pardhuvarmax/Project-Ouroboros/BluePill/Documentations/Ouroboros Roles Doc.pdf

# Project Ouroboros – Roles & Responsibilities Document

## Overview

Project Ouroboros is a dual-nature cybersecurity + hardware + AI initiative that embodies the eternal cycle of attack and defense, inspired by the mythological serpent Ouroboros. To ensure the successful execution of this project, clear roles and responsibilities are essential across technical, strategic, and business domains.

This document defines all roles required for the development, launch, and scaling of Project Ouroboros, with responsibilities spanning hardware, software, AI, research, community engagement, and commercialization.

## 1. Leadership & Governance

Project Lead (Founder / Visionary)

Define overall vision and mission of Project Ouroboros.
Oversee both defensive and offensive components, ensuring balance. Make final decisions on product scope, direction, and partnerships. Maintain philosophical and mythological branding rooted in Ouroboros. Ensure legal and ethical compliance.
Advisory Board (Mentors / Senior Experts)

Provide expert advice on cybersecurity, hardware, AI, and product strategy. Ensure project aligns with academic, industrial, and ethical standards. Connect with investors, Kickstarter advisors, and community leaders.

## 2. Technical Development

Hardware Engineering Team

Design PCB schematics and layouts for ESP32 + SDR devices. Integrate display modules (OLED, TFT, touchscreen).
Ensure low-cost, reliable builds for Kickstarter scalability. Prototype RF-based tools (BLE sniffer, Sub-GHz jammer, etc.). Firmware Development Team

Develop embedded C / Arduino / MicroPython firmware for ESP32. Implement features:
Wi-Fi deauth detector & shield.
Spectrum analyzer (2.4 GHz).

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
BLE sniffing & spoof detection.
RF scanning & replay attack modules.
Optimize for low power consumption and smooth real-time graphs. Software & AI Development Team

Build AI-based anomaly detection models (TinyML on-device or cloud). Develop companion mobile/desktop app for visualization & extended analysis. Implement real-time packet analysis, rogue detection, and network hardening. Secure communication channel between devices and apps.
Cybersecurity Research Team

Research latest Wi-Fi, BLE, Zigbee, Sub-GHz vulnerabilities.
Test and validate offensive tools (beacon spammer, captive portal, replay attacks). Ensure defensive tools are hardened against evolving threats.
Document open-source offensive modules for GitHub community.

## 3. Product & UX

UI/UX Design Team

Create intuitive interfaces for TFT/OLED displays.
Design real-time waterfall graphs for spectrum analyzers. Build smooth UX for mobile companion app.
Ensure defensive device feels professional & consumer-friendly. Product Management

Define roadmap: pre-release, Kickstarter launch, v2 upgrades.
Balance feature sets between defense (consumer market) and offense (research GitHub). Conduct competitor benchmarking (Flipper Zero, Wi-Fi Pineapple, etc.).
Ensure pricing strategy aligns with build cost and market demand.

## 4. Business & Commercialization

Kickstarter Campaign Manager

Develop and manage the crowdfunding campaign.
Create marketing materials, videos, and product storytelling. Manage tiered pricing, stretch goals, and reward structures. Oversee logistics for backer rewards.
Branding & Marketing Team

Create strong brand identity rooted in Ouroboros mythology. Manage social media campaigns, community engagement, and PR. Collaborate with YouTubers, infosec influencers, and educators. Highlight defensive device as consumer-friendly.

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
Sales & Distribution

Handle pre-orders, shipping, and customer support post-Kickstarter. Work with global distributors for scaling production.
Partner with academic institutions & cybersecurity educators.

## 5. Community & Recognition

Open Source Offensive Team

Maintain GitHub repository for offensive research tools. Provide documentation, tutorials, and safe-use guidelines. Encourage collaboration with cybersecurity researchers.
Community Manager

Engage with Kickstarter backers, GitHub contributors, and Discord/Reddit communities. Host Q&A, demos, and feedback loops.
Build trust with both consumer and hacker communities.
Recognition Strategy Lead

Pitch defensive side to Kickstarter/consumers.
Promote offensive side to hacking/research communities.
Submit papers to cybersecurity conferences.
Engage with anti-scam creators (e.g., Scammers Payback) for visibility.

## 6. Legal & Ethics

Legal Advisor

Ensure compliance with international export control laws (FCC, CE, ITAR, etc.).
Manage licenses, disclaimers, and liability shields.
Differentiate clearly between consumer defense product (commercial) and offensive tools (educational research, non-commercial).
Ethics & Oversight Committee

Define boundaries for offensive features.
Ensure transparency with users on legal use cases. Prevent misuse by building safeguards (kill switches, limits).

## 7. Operations & Finance

Operations Manager

Oversee supply chain for ESP32, SDR, and display modules.

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
Handle PCB production, QA testing, and scaling manufacturing. Manage vendor relationships and logistics.
Finance Manager

Estimate and track build costs per unit.
Define retail pricing strategy (₹3,000–₹5,000 per unit for defense device). Plan budget for Kickstarter video, marketing, and production.
Manage cash flow from Kickstarter to post-launch operations.

## 8. Future Expansion Roles

AI Research Lead – For on-device ML advancement.
Cloud Infrastructure Lead – For companion apps and remote dashboards.
Educational Partnerships Coordinator – To integrate devices into cybersecurity curricula. Product Evangelists – To represent Ouroboros at global conferences.

## Conclusion

Project Ouroboros thrives on balance—just as the serpent devours itself to sustain eternity, the project sustains its ecosystem by uniting defense and offense. This roles and responsibilities framework ensures clarity, accountability, and structured growth.

By maintaining synergy across technical innovation, consumer trust, and research recognition, Ouroboros can evolve into a landmark cybersecurity project symbolizing the eternal cycle of protection and discovery.

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
