pardhuvarmax/Project-Ouroboros/BluePill/Documentations/Ouroboros.pdf

# Project Ouroboros

## Introduction

Project Ouroboros is a dual-nature cybersecurity + hardware + AI initiative inspired by the mythological serpent Ouroboros, the eternal cycle of life, death, creation, and destruction. It symbolizes balance and recursion — here mapped onto cybersecurity’s endless cycle of attack and defense. The project embodies this duality:

Defensive Side: A consumer-friendly, Kickstarter-ready device to protect against wireless attacks.
Offensive Side: A set of open-source offensive cybersecurity tools for researchers and ethical hackers.

This document provides an encyclopedic overview of the project — its mythological foundation, technical architecture, features, hardware and software stack, cost strategies, monetization plans, and recognition pathways.

## Mythological Foundation

Ouroboros (Greek/Egyptian Myth): An ancient symbol depicting a serpent eating its own tail, representing eternity, cyclic renewal, balance of life and death.
Cybersecurity Context: The endless loop of attackers evolving new exploits and defenders adapting with new protections. Project Ouroboros represents this cycle embodied in hardware + AI form.
Duality: Just as Ouroboros contains itself, this project contains both:
Defensive creation (protection, resilience)
Offensive destruction (research, attack simulations)

## Core Concept

Project Ouroboros is split into two complementary branches:

### 1. Defensive Side (Kickstarter, consumer-focused)

Goal: Protect consumers, small businesses, and enthusiasts from wireless attacks. Platform: ESP32-based device with full TFT/OLED display.
Features:
Wi-Fi Deauth Attack Shield: Detects and blocks Wi-Fi deauthentication floods. Wi-Fi Scanner: Lists nearby networks with extended details.
Spectrum Analyzer (2.4GHz): Scans 128 channels (Wi-Fi, Zigbee, custom RF).
Packet Monitor: Real-time waterfall graph of all 14 Wi-Fi channels.
BLE Sniffer: Detects BLE and Classic Bluetooth devices.
Threat Detection: Identifies suspicious behaviors (jamming, MAC spoofing, beacon spoofing). Alerts System: Visual + sound notifications for real-time threats.

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
Display: TFT full-color screen with graphical UI.
AI/ML: TinyML on ESP32 or companion app for anomaly classification.

### 2. Offensive Side (open-source, GitHub)

Goal: Provide cybersecurity researchers and enthusiasts with attack simulation tools. Platform: ESP32 + SDR modules (HackRF, RTL-SDR).
Features:
Packet Monitor (waterfall graphing).
Beacon Spammer (fake AP flooding).
Wi-Fi Deauthenticator (with touchscreen UI). Captive Portal (credential harvesting demo). BLE Jammer & Spoofer.
BLE Scanner.
Protokill (2.4GHz jamming: Zigbee, Wi-Fi).
Replay Attack Module (Sub-GHz signals like garage remotes). Sub-GHz Jammer.
Saved Profiles (store/replay captured signals).
RF Spectrum Analyzer.

## Hardware Platforms

Core MCU: ESP32 (Wi-Fi + BLE + low power + cheap). Companion Hardware:
TFT/OLED screen (UI + visualization).
SDR devices (HackRF One, RTL-SDR).
Sub-GHz RF modules (CC1101, NRF24L01). Optional Expansion:
Battery pack for portability.
External antennas for range extension. Case/housing for consumer-ready design.

## Software Stack

Defensive Side:
C/C++ firmware for ESP32.
TinyML models for anomaly detection.
Optional Android/iOS companion app for extended visualization. Offensive Side:
ESP32 firmware with modular attack modes.
Python libraries for SDR integration.
Web dashboard for visualization/logging.

## Cost & Production Strategy

Prototype Cost: \$20–\$30 (ESP32 \$5, TFT screen \$5–\$10, misc RF modules \$5–\$15). Mass Build Cost: Reduced to \$10–\$15 per unit with bulk manufacturing.

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
Kickstarter Pricing:
Early Bird: ₹2,000 (\$25)
Standard Retail: ₹3,500–5,000 (\$40–\$60)
Offensive Side Cost: Zero retail (open-source on GitHub).

Detailed Estimate :

ESP32 board: ₹400–500 (\$5–\$6)
Display (OLED): ₹250–400 (\$3–\$5)
TFT touchscreen: ₹800–1,200 (\$10–\$15)
SDR dongle (optional): ₹2,500–3,500 (\$30–\$40)
Misellaneous (battery, casing, antennas): ₹500–1,000 (\$6–\$12)

Prototype Build Cost:

Basic defensive device: ₹1,500–2,000 (\$20–\$25)
Premium defensive device: ₹2,500–3,500 (\$30–\$40)

Kickstarter Retail Price:

Basic: ₹3,000–3,500 (\$40–\$45)
Premium: ₹4,000–5,000 (\$50–\$65)

## Monetization Plan

Defensive Device:
Sell via Kickstarter and later through e-commerce platforms. Bundle with a mobile app (freemium advanced analytics).
Offensive Device:
Open-source → recognition in hacker/research community.
Boosts credibility, attracts collaborations, speaking invites, partnerships.

## Recognition & Branding Strategy

Dual Identity:
Defensive Side: Safe, consumer-protective branding.
Offensive Side: Research-focused, hacker-community branding. Influencer Outreach:
Cybersecurity YouTubers (Scammer-revenge, infosec educators). Hacker conferences (DEFCON, Black Hat, Nullcon).
Philosophy Alignment:
Balance between protection and exposure.
"The eternal cycle of attack and defense."
Logo Concept:
A serpent (Ouroboros) forming a circuit loop, tail in mouth, encircling Wi-Fi waves.

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
## Advantages of Project Ouroboros

Low-cost build → high profit margin.
Strong mythic branding → memorable, iconic. Appeals to dual audiences:
Consumers (defensive tool).
Hackers/researchers (offensive open source).
Scalable → expand to Sub-GHz, 5GHz, AI-driven upgrades. Community-driven → open-source contribution and Kickstarter buzz.

## Roadmap

Phase 1 (0–2 months): Prototype on ESP32 + TFT, test defensive Wi-Fi shield.
Phase 2 (3–5 months): Add BLE sniffer, spectrum analyzer, ML threat detection.
Phase 3 (6–8 months): Offensive side tools (deauth, beacon spamming, replay attack). Phase 4 (9–12 months): Kickstarter launch, influencer marketing, DEFCON demo.

Future Developments & Scope.

Gen-1/Prototype-1 (Now):

ESP32 + TFT display defensive device. Offensive open-source Wi-Fi/Bluetooth suite.

Gen-2:

Integration with SDR for Sub-GHz and wideband RF tools. AI-powered auto-mitigation.
Cloud dashboard companion app.

Gen-3:

Full ecosystem with modular plug-ins.
Enterprise edition for network security monitoring.

## Summary

Project Ouroboros is a dual-path innovation in cybersecurity hardware:

A Kickstarter-ready defensive tool to protect against wireless threats.
An open-source offensive toolkit for research and recognition.
Inspired by the eternal myth of Ouroboros, it embodies the cycle of attack and defense.

With low costs, strong branding, dual monetization, and community appeal, Ouroboros stands as both a business opportunity and a research landmark in cyber-physical security.

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
## See Also

Ouroboros (Mythology)
ESP32 Security Research
HackRF / RTL-SDR Projects
DEFCON Hardware Hacking Village

•
•
•
•
