pardhuvarmax/Project-Ouroboros/OuroMini/dashboard/webapp/espwebserver/README.md

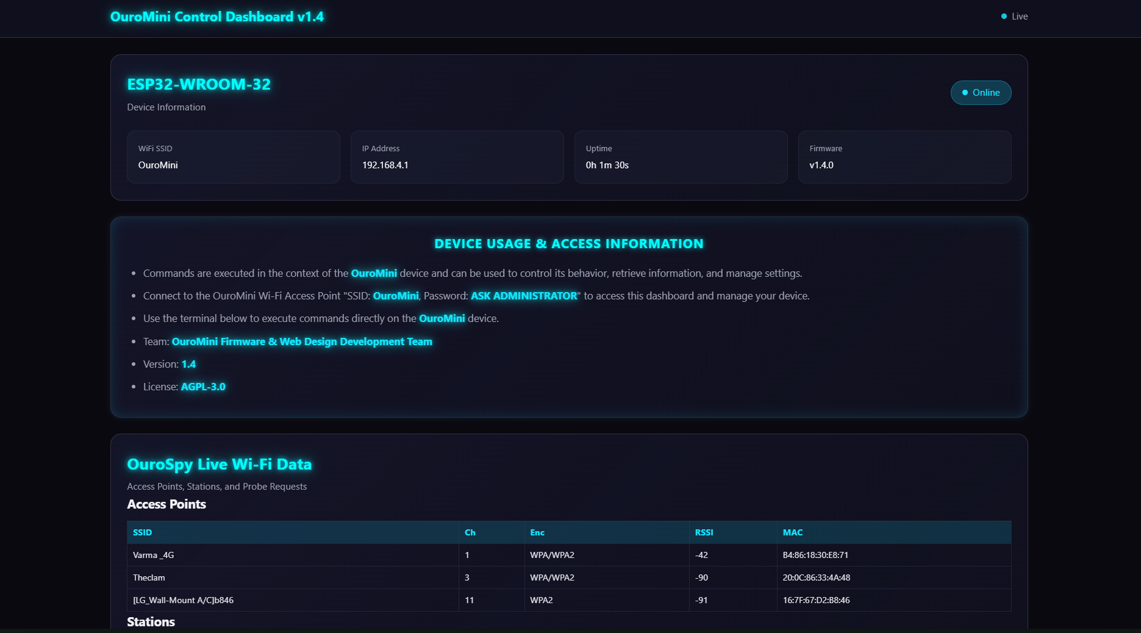
[picture p51: OuroMini/dashboard/webapp/espwebserver/page1.png]

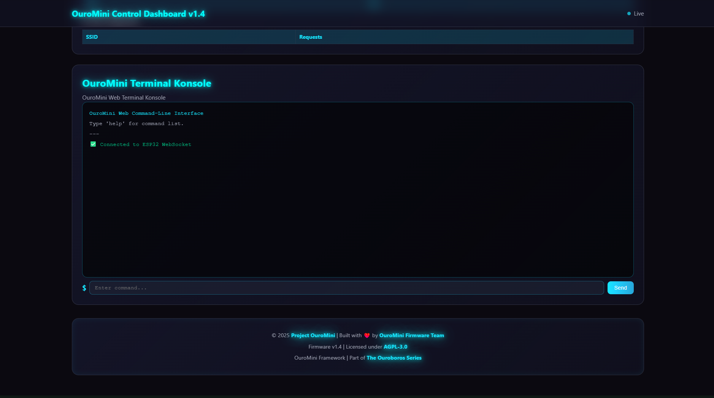
[picture p52: OuroMini/dashboard/webapp/espwebserver/page2.png]
