pardhuvarmax/Project-Ouroboros/OuroMini/dashboard/webapp/ouromini-webui/docs/homepage.png

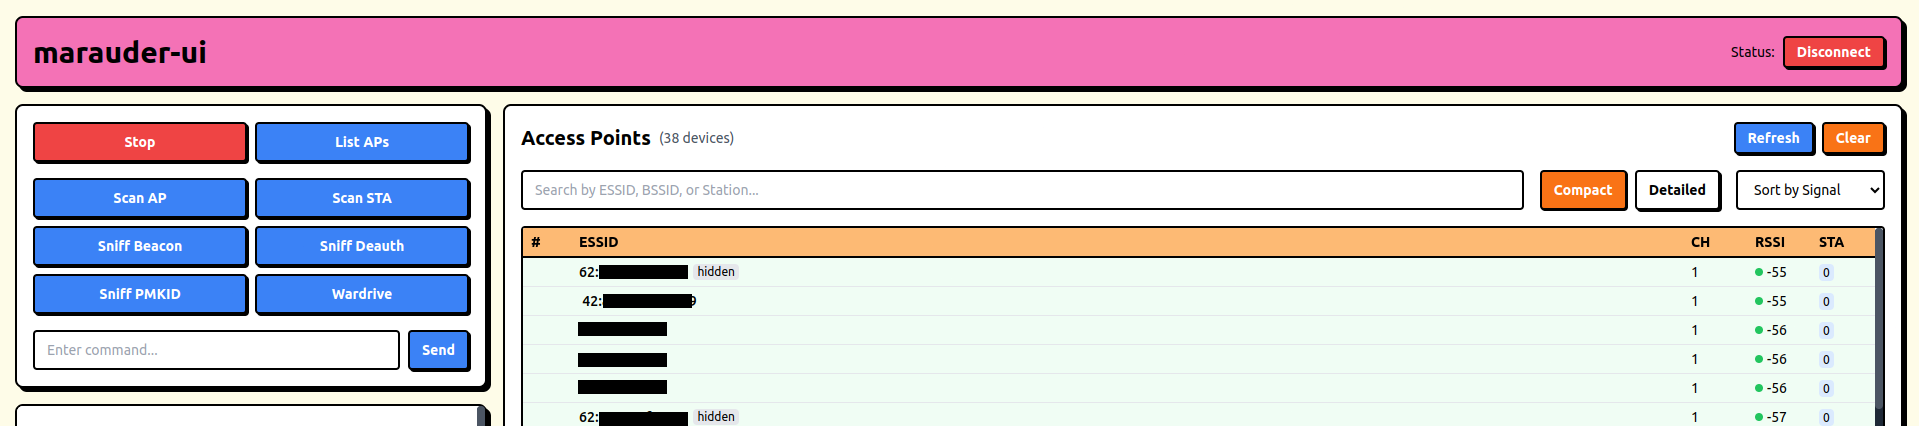
OuroMini/dashboard/webapp/ouromini-webui/docs/homepage.png
