pardhuvarmax/Project-Ouroboros/OuroMini/media/IMG_20250820_135714300.jpg

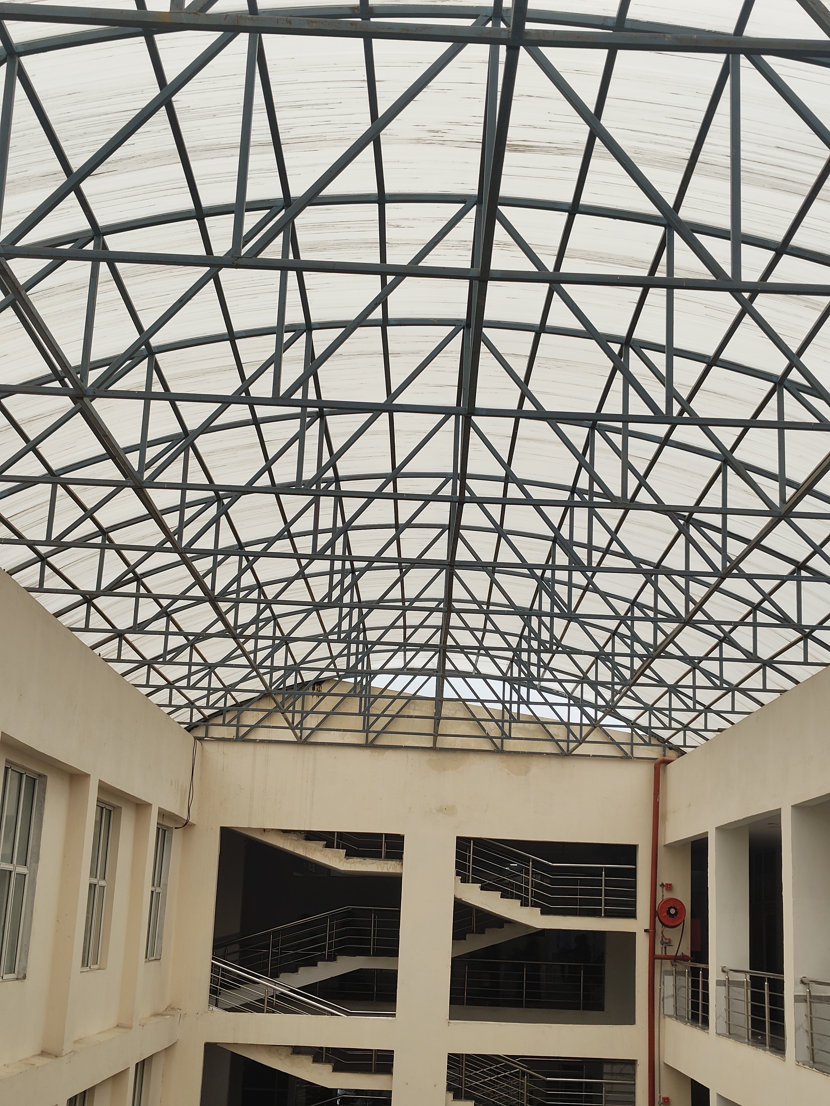
OuroMini/media/IMG_20250820_135714300.jpg
