pardhuvarmax/Project-Ouroboros/OuroMini/media/IMG_20250909_132152491.jpg

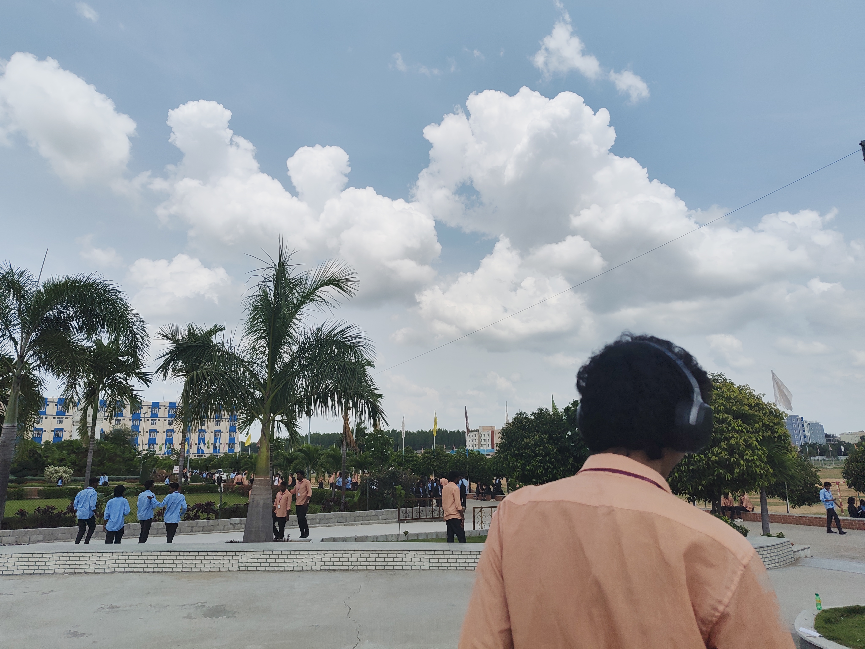
OuroMini/media/IMG_20250909_132152491.jpg
