pardhuvarmax/Project-Ouroboros/OuroMini/media/IMG_20251010_142202657.jpg

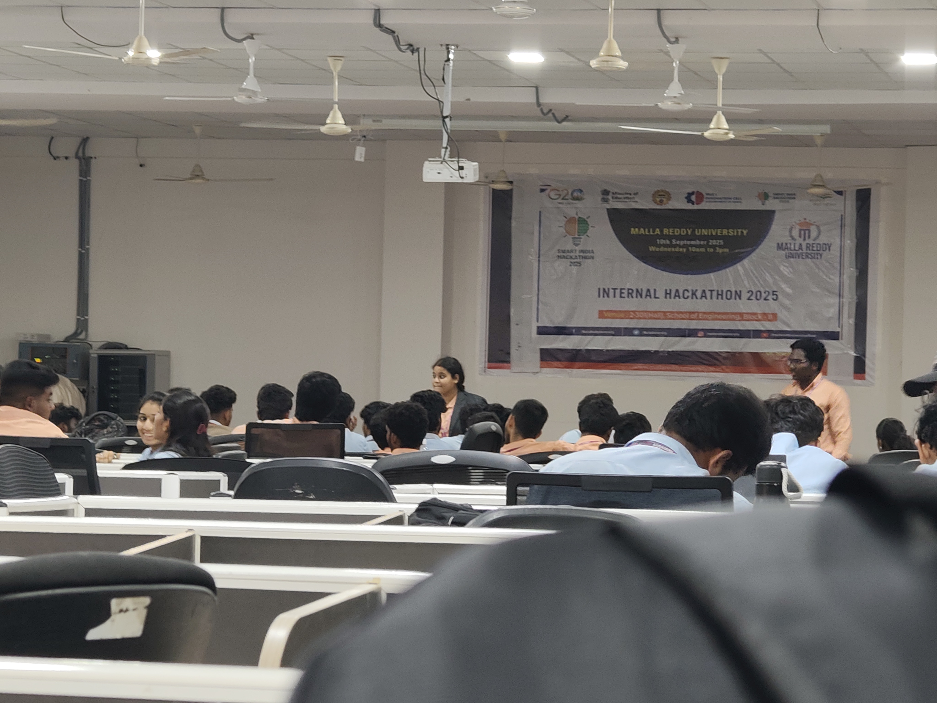
OuroMini/media/IMG_20251010_142202657.jpg
