pardhuvarmax/Project-Ouroboros/OuroMini/media/IMG_20251010_150730520.jpg

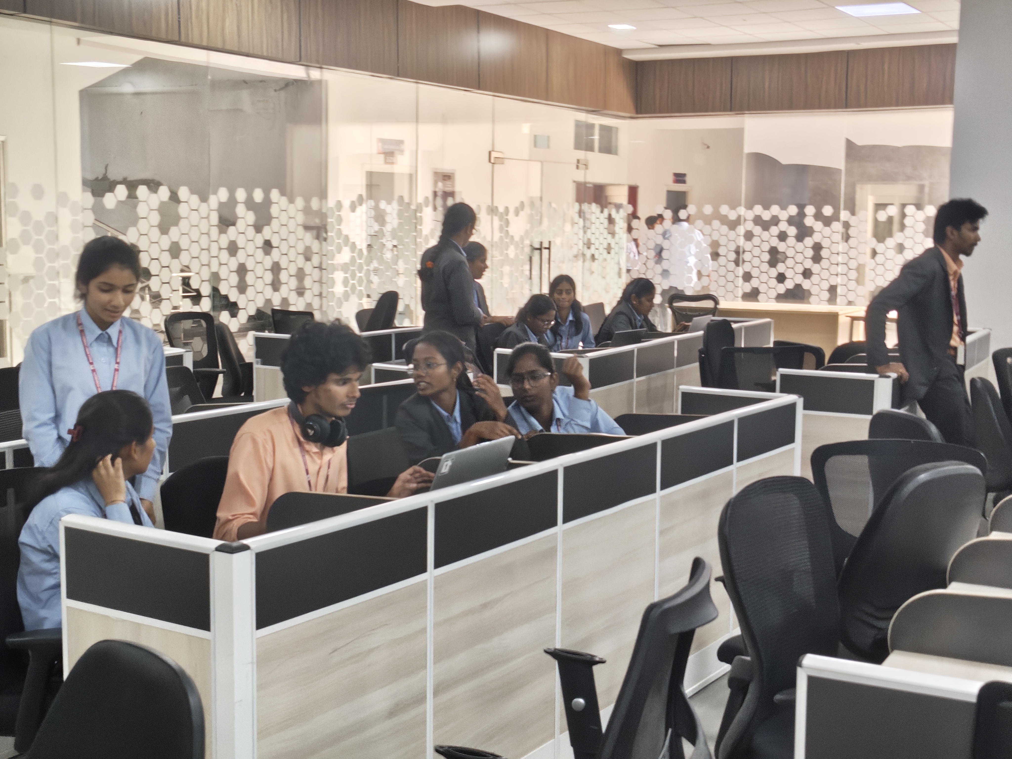
OuroMini/media/IMG_20251010_150730520.jpg
