pardhuvarmax/Project-Ouroboros/OuroMini/media/IMG_20251029_133743349 (1).jpg

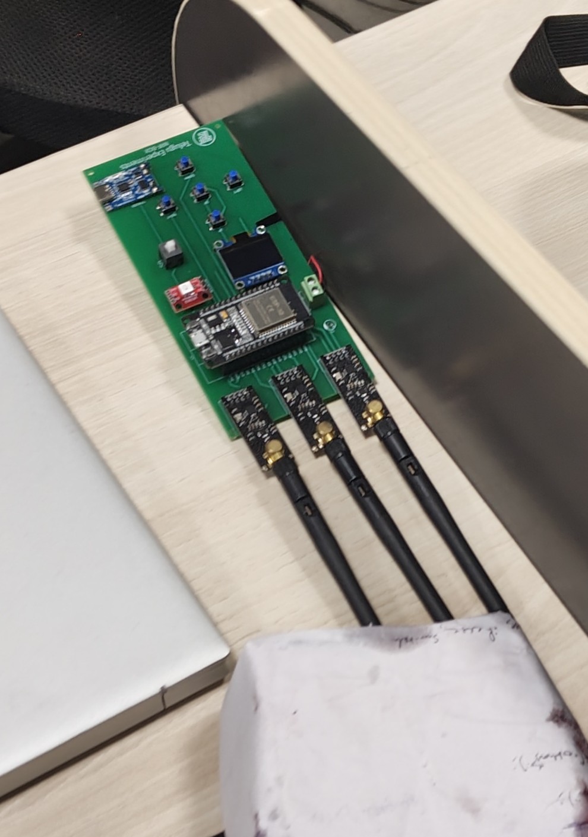
OuroMini/media/IMG_20251029_133743349 (1).jpg
