pardhuvarmax/Project-Ouroboros/OuroMini/media/IMG_20251101_131902682.jpg

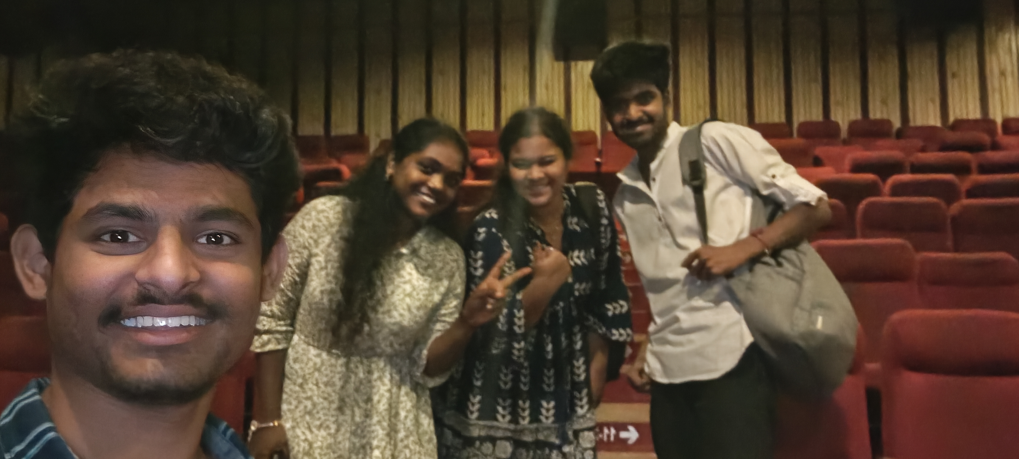
OuroMini/media/IMG_20251101_131902682.jpg
