pardhuvarmax/Project-Ouroboros/OuroMini/media/IMG_20251103_134154348.jpg

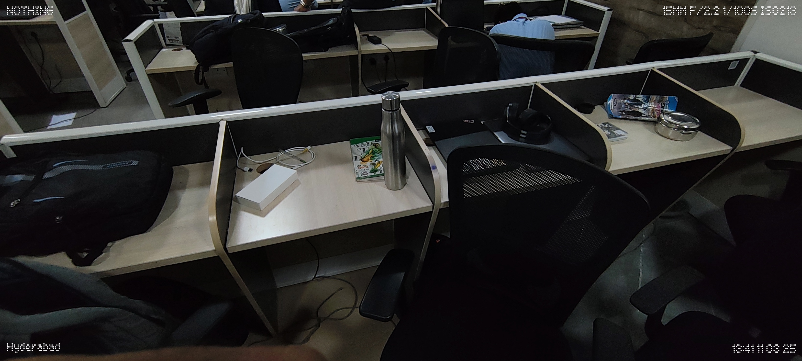
OuroMini/media/IMG_20251103_134154348.jpg
