pardhuvarmax/Project-Ouroboros/OuroMini/media/IMG_20251103_140503418.jpg

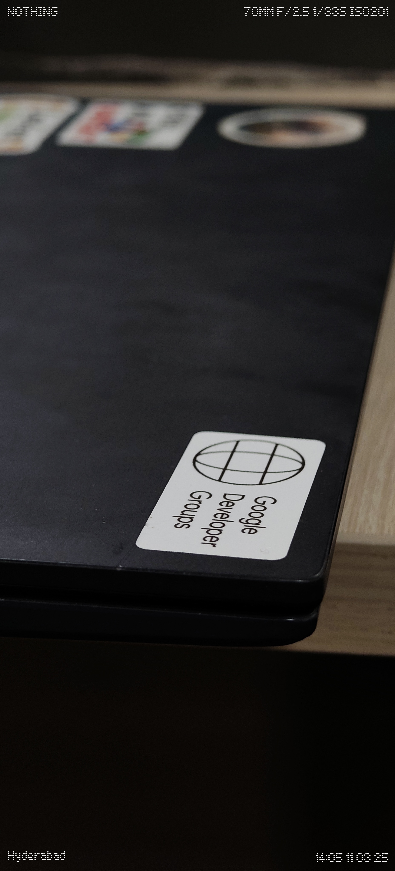
OuroMini/media/IMG_20251103_140503418.jpg
