pardhuvarmax/Project-Ouroboros/OuroMini/media/IMG_20251103_141946841.jpg

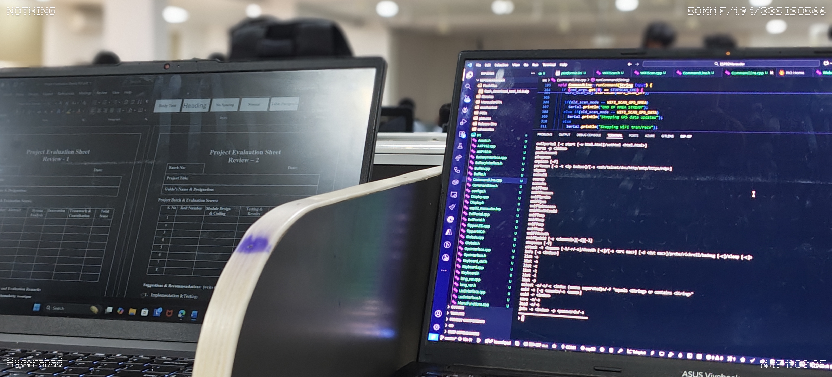
OuroMini/media/IMG_20251103_141946841.jpg
