pardhuvarmax/Project-Ouroboros/OuroMini/media/IMG_20251103_142009825.jpg

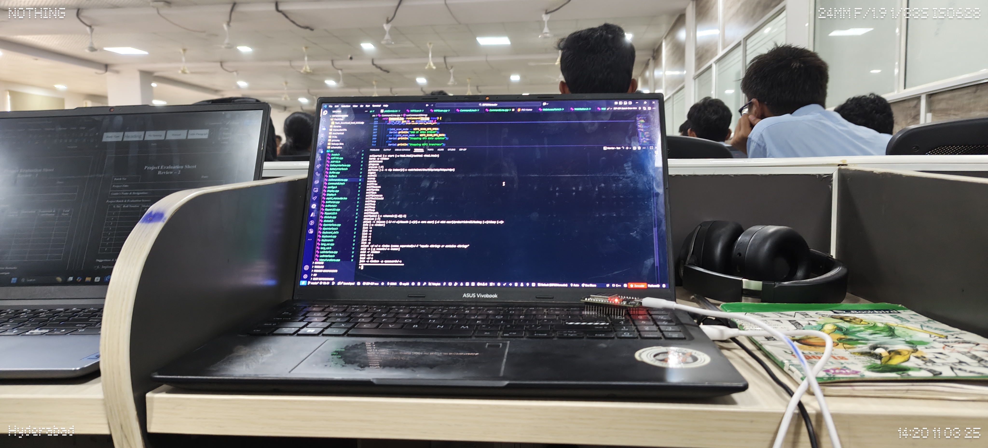
OuroMini/media/IMG_20251103_142009825.jpg
