pardhuvarmax/Project-Ouroboros/OuroMini/media/IMG_20251103_222805060.jpg

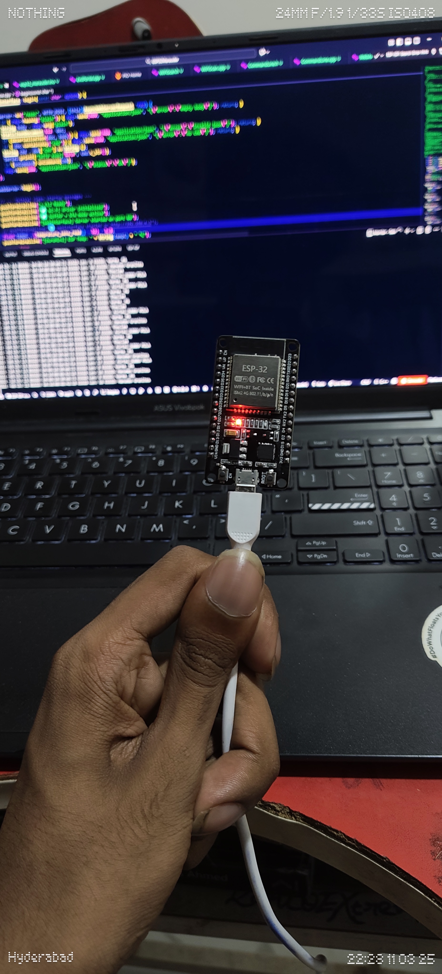
OuroMini/media/IMG_20251103_222805060.jpg
