pardhuvarmax/Project-Ouroboros/OuroMini/media/IMG_20251104_100048495.jpg

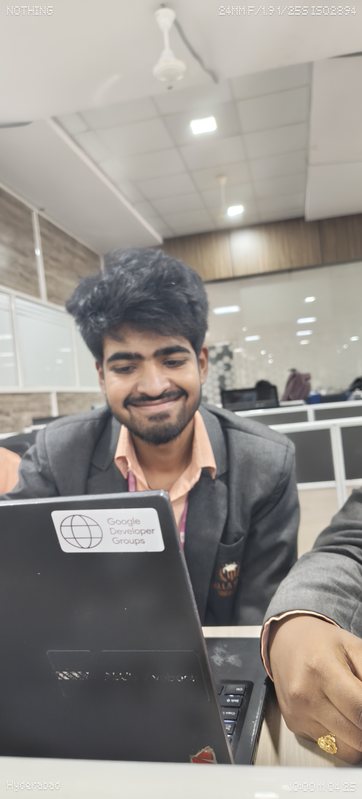
OuroMini/media/IMG_20251104_100048495.jpg
