pardhuvarmax/Project-Ouroboros/OuroMini/media/IMG_20251104_134605800.jpg

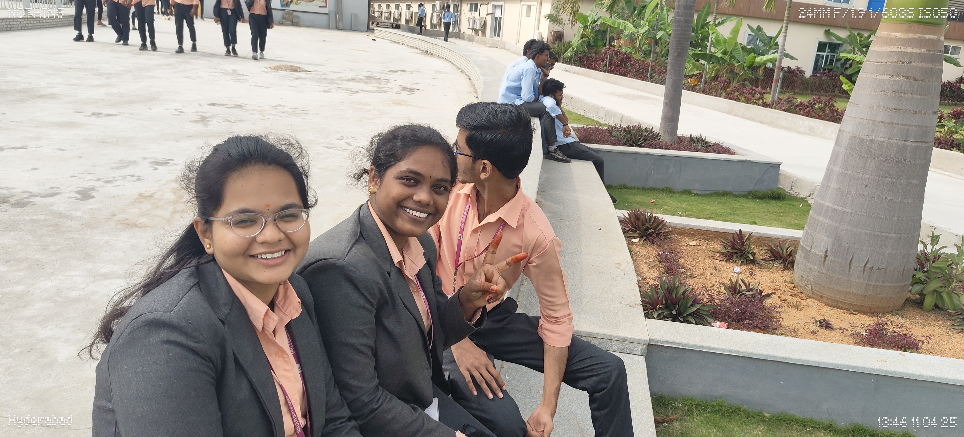
OuroMini/media/IMG_20251104_134605800.jpg
