pardhuvarmax/Project-Ouroboros/OuroMini/media/IMG_20251108_133215504.jpg

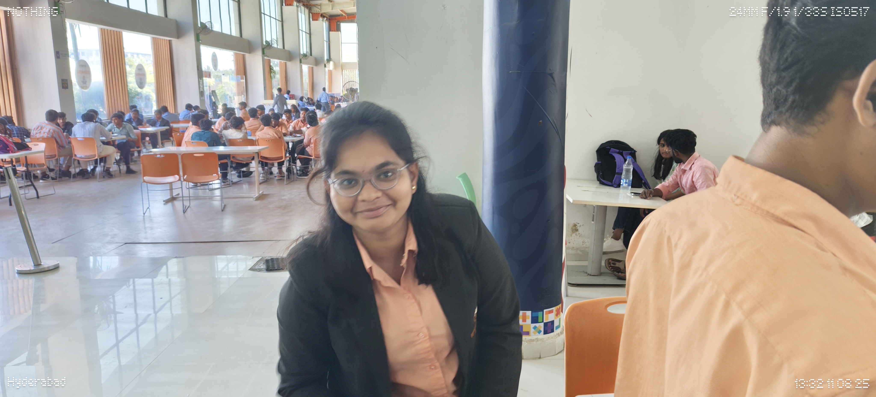
OuroMini/media/IMG_20251108_133215504.jpg
