pardhuvarmax/Project-Ouroboros/OuroMini/media/Screenshot_20251104-153046.png

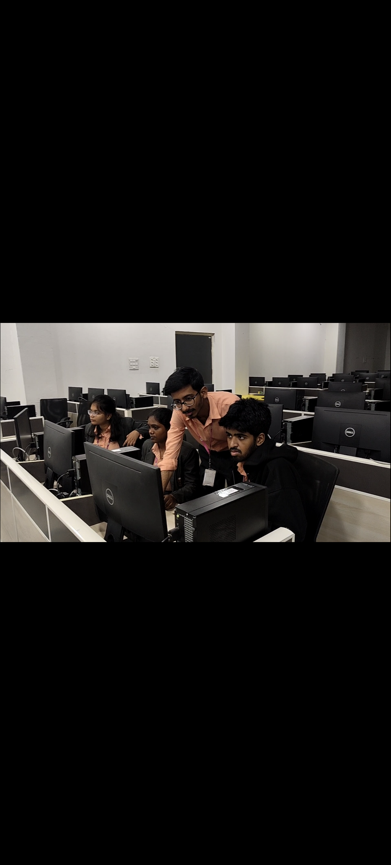
OuroMini/media/Screenshot_20251104-153046.png
