pardhuvarmax/Project-Ouroboros/OuroMini/firmware/source/ouis.h

#ifndef OUIS_H
#define OUIS_H

#include <Arduino.h>

// ----------------------- Apple OUIs -----------------------
const char apple_ouis[][9] PROGMEM = {
  "00:17:F2", "00:1E:C2", "00:26:08", "F8:1E:DF", "BC:92:6B", 
  "28:E0:2C", "3C:07:54", "7C:D1:C3", "DC:A9:04", "F0:D1:A9",
  "C0:2C:5C", "00:03:93", "00:03:94", "00:03:95", "00:03:96",
  "00:03:97", "00:03:98", "00:03:99", "00:03:9A", "00:03:9B",
  "00:03:9C", "00:03:9D", "00:03:9E", "00:03:9F", "00:03:A0",
  "00:03:A1", "00:03:A2", "00:03:A3", "00:03:A4", "00:03:A5",
  "00:03:A6", "00:03:A7", "00:03:A8", "00:03:A9", "00:03:AA",
  "00:03:AB", "00:03:AC", "00:03:AD", "00:03:AE", "00:03:AF",
  "00:03:B0", "00:03:B1", "00:03:B2", "00:03:B3", "00:03:B4",
  "00:03:B5", "00:03:B6", "00:03:B7", "00:03:B8", "00:03:B9",
  "00:03:BA", "00:03:BB", "00:03:BC", "00:03:BD", "00:03:BE",
  "00:03:BF", "00:03:C0", "00:03:C1", "00:03:C2", "00:03:C3",
  "00:03:C4", "00:03:C5", "00:03:C6", "00:03:C7", "00:03:C8",
  "00:03:C9", "00:03:CA", "00:03:CB", "00:03:CC", "00:03:CD",
  "00:03:CE", "00:03:CF", "00:03:D0", "00:03:D1", "00:03:D2",
  "00:03:D3", "00:03:D4", "00:03:D5", "00:03:D6", "00:03:D7",
  "00:03:D8", "00:03:D9", "00:03:DA", "00:03:DB", "00:03:DC",
  "00:03:DD", "00:03:DE", "00:03:DF", "00:03:E0", "00:03:E1",
  "00:03:E2", "00:03:E3", "00:03:E4", "00:03:E5", "00:03:E6",
  "00:03:E7", "00:03:E8", "00:03:E9", "00:03:EA", "00:03:EB",
  "00:03:EC", "00:03:ED", "00:03:EE", "00:03:EF", "00:03:F0",
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
  "28:C2:DD", "2C:54:CF", "30:23:03", "34:CE:00", "38:2C:4A", 
  "40:16:7E", "48:5B:39", "50:46:5D", "5C:57:CE", "60:67:20", 
  "64:70:02", "70:4D:7B", "78:24:AF", "7C:11:CC", "80:7D:3A", 
  "84:38:35", "88:32:9B", "8C:3A:E3", "90:B1:1C", "94:65:2D"
};

// ----------------------- Xiaomi OUIs -----------------------
const char xiaomi_ouis[][9] PROGMEM = {
  "04:CF:8C", "28:6C:07", "3C:71:BF", "44:65:0D", "5C:49:79", 
  "64:16:66", "68:27:37", "74:4D:28", "78:11:DC", "7C:49:EB", 
  "84:CC:A8", "88:6B:0F", "8C:AA:B5", "9C:65:3A", "A0:14:3D", 
  "AC:BC:32", "B4:CE:F6", "C0:EE:FB", "C8:3A:35", "D4:CA:6D"
};

#endif // OUIS_H
