pardhuvarmax/Project-Ouroboros/OuroMini/firmware/source/lang_var.h

#pragma once
#ifndef LANG_VAR_H
#define LANG_VAR_H

#include "configs.h"
#include <Arduino.h>

// Starting window texts
extern const char text0_0[] PROGMEM;
extern const char text0_1[] PROGMEM;
extern const char text0_2[] PROGMEM;
extern const char text0_3[] PROGMEM;
extern const char text0_4[] PROGMEM;
extern const char text0_5[] PROGMEM;
extern const char text0_6[] PROGMEM;
extern const char text0_7[] PROGMEM;
extern const char text0_8[] PROGMEM;

// Single library texts/Often used
extern const char text00[] PROGMEM;
extern const char text01[] PROGMEM;
extern const char text02[] PROGMEM;
extern const char text03[] PROGMEM;
extern const char text04[] PROGMEM;
extern const char text05[] PROGMEM;
extern const char text06[] PROGMEM;
extern const char text07[] PROGMEM;
extern const char text08[] PROGMEM;
extern const char text09[] PROGMEM;
extern const char text10[] PROGMEM;
extern const char text11[] PROGMEM;
extern const char text12[] PROGMEM;
extern const char text13[] PROGMEM;
extern const char text14[] PROGMEM;
extern const char text15[] PROGMEM;
extern const char text16[] PROGMEM;
extern const char text17[] PROGMEM;
extern const char text18[] PROGMEM;

// MenuFunctions.cpp texts
extern const char text1_0[] PROGMEM;
extern const char text1_1[] PROGMEM;
extern const char text1_2[] PROGMEM;
extern const char text1_3[] PROGMEM;
extern const char text1_4[] PROGMEM;
extern const char text1_5[] PROGMEM;
extern const char text1_6[] PROGMEM;
extern const char text1_7[] PROGMEM;
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
extern const char text4_49[] PROGMEM;

// Tables
extern const char* const text_table0[] PROGMEM;
extern const char* const text_table1[] PROGMEM;
extern const char* const text_table2[] PROGMEM;
extern const char* const text_table3[] PROGMEM;
extern const char* const text_table4[] PROGMEM;

#endif
