pardhuvarmax/Project-Ouroboros/OuroMini/firmware/source/WiFiScan.cpp

#include "esp_random.h"
#include "WiFiScan.h"
#include "lang_var.h"
#include "Globals.h"

#ifdef HAS_PSRAM
  struct mac_addr* mac_history = nullptr;
#endif

int num_beacon = 0;
int num_deauth = 0;
int num_probe = 0;
int num_eapol = 0;

LinkedList<ssid>* ssids;
LinkedList<AccessPoint>* access_points;
LinkedList<AirTag>* airtags;
LinkedList<Flipper>* flippers;
LinkedList<IPAddress>* ipList;
LinkedList<ProbeReqSsid>* probe_req_ssids;

extern "C" int my_ieee_check(int32_t arg, int32_t arg2, int32_t arg3){
    if (arg == 31337)
      return 1;
    else
      return 0;
}

extern "C" {
  uint8_t esp_base_mac_addr[6];
  esp_err_t esp_ble_gap_set_rand_addr(const uint8_t *rand_addr);
}

#ifdef HAS_BT
  //ESP32 Sour Apple by RapierXbox
  //Exploit by ECTO-1A
  NimBLEAdvertising *pAdvertising;

  //// https://github.com/Spooks4576
  NimBLEAdvertisementData WiFiScan::GetUniversalAdvertisementData(EBLEPayloadType Type) {
    NimBLEAdvertisementData AdvData = NimBLEAdvertisementData();

    uint8_t* AdvData_Raw = nullptr;
    uint8_t i = 0;

    switch (Type) {
      case Microsoft: {
        
        const char* Name = generateRandomName();

        uint8_t name_len = strlen(Name);

        AdvData_Raw = new uint8_t[7 + name_len];

        AdvData_Raw[i++] = 7 + name_len - 1;
        AdvData_Raw[i++] = 0xFF;
        AdvData_Raw[i++] = 0x06;
        AdvData_Raw[i++] = 0x00;
        AdvData_Raw[i++] = 0x03;
        AdvData_Raw[i++] = 0x00;
        AdvData_Raw[i++] = 0x80;
        memcpy(&AdvData_Raw[i], Name, name_len);
        i += name_len;

        AdvData.addData(std::string((char *)AdvData_Raw, 7 + name_len));
        break;
      }
      case Apple: {
        AdvData_Raw = new uint8_t[17];

        AdvData_Raw[i++] = 17 - 1;    // Packet Length
        AdvData_Raw[i++] = 0xFF;        // Packet Type (Manufacturer Specific)
        AdvData_Raw[i++] = 0x4C;        // Packet Company ID (Apple, Inc.)
        AdvData_Raw[i++] = 0x00;        // ...
        AdvData_Raw[i++] = 0x0F;  // Type
        AdvData_Raw[i++] = 0x05;                        // Length
        AdvData_Raw[i++] = 0xC1;                        // Action Flags
        const uint8_t types[] = { 0x27, 0x09, 0x02, 0x1e, 0x2b, 0x2d, 0x2f, 0x01, 0x06, 0x20, 0xc0 };
        AdvData_Raw[i++] = types[rand() % sizeof(types)];  // Action Type
        esp_fill_random(&AdvData_Raw[i], 3); // Authentication Tag
        i += 3;   
        AdvData_Raw[i++] = 0x00;  // ???
        AdvData_Raw[i++] = 0x00;  // ???
        AdvData_Raw[i++] =  0x10;  // Type ???
        esp_fill_random(&AdvData_Raw[i], 3);

        AdvData.addData(std::string((char *)AdvData_Raw, 17));
        break;
      }
      case Samsung: {

        AdvData_Raw = new uint8_t[15];

        uint8_t model = watch_models[rand() % 25].value;
        
        AdvData_Raw[i++] = 14; // Size
        AdvData_Raw[i++] = 0xFF; // AD Type (Manufacturer Specific)
        AdvData_Raw[i++] = 0x75; // Company ID (Samsung Electronics Co. Ltd.)
        AdvData_Raw[i++] = 0x00; // ...
        AdvData_Raw[i++] = 0x01;
        AdvData_Raw[i++] = 0x00;
        AdvData_Raw[i++] = 0x02;
        AdvData_Raw[i++] = 0x00;
        AdvData_Raw[i++] = 0x01;
        AdvData_Raw[i++] = 0x01;
        AdvData_Raw[i++] = 0xFF;
        AdvData_Raw[i++] = 0x00;
        AdvData_Raw[i++] = 0x00;
        AdvData_Raw[i++] = 0x43;
        AdvData_Raw[i++] = (model >> 0x00) & 0xFF; // Watch Model / Color (?)

        AdvData.addData(std::string((char *)AdvData_Raw, 15));

        break;
      }
      case Google: {
        AdvData_Raw = new uint8_t[14];
        AdvData_Raw[i++] = 3;
        AdvData_Raw[i++] = 0x03;
        AdvData_Raw[i++] = 0x2C; // Fast Pair ID
        AdvData_Raw[i++] = 0xFE;

        AdvData_Raw[i++] = 6;
        AdvData_Raw[i++] = 0x16;
        AdvData_Raw[i++] = 0x2C; // Fast Pair ID
        AdvData_Raw[i++] = 0xFE;
        AdvData_Raw[i++] = 0x00; // Smart Controller Model ID
        AdvData_Raw[i++] = 0xB7;
        AdvData_Raw[i++] = 0x27;

        AdvData_Raw[i++] = 2;
        AdvData_Raw[i++] = 0x0A;
        AdvData_Raw[i++] = (rand() % 120) - 100; // -100 to +20 dBm

        AdvData.addData(std::string((char *)AdvData_Raw, 14));
        break;
      }
      case FlipperZero: {
        // Generate a random 5-letter name for the advertisement
        char Name[6];  // 5 characters + null terminator
        generateRandomName(Name, sizeof(Name));

        uint8_t name_len = strlen(Name);

        // Allocate space for the full Advertisement Data section based on the hex dump
        AdvData_Raw = new uint8_t[31];  // Adjusted to the specific length of the data in the dump

        // Advertisement Data from the hex dump
        AdvData_Raw[i++] = 0x02;  // Flags length
        AdvData_Raw[i++] = 0x01;  // Flags type
        AdvData_Raw[i++] = 0x06;  // Flags value

        AdvData_Raw[i++] = 0x06;  // Name length (5 + type)
        AdvData_Raw[i++] = 0x09;  // Complete Local Name type

        // Add the randomized 5-letter name
        memcpy(&AdvData_Raw[i], Name, name_len);
        i += name_len;

        AdvData_Raw[i++] = 0x03;  // Incomplete List of 16-bit Service UUIDs length
        AdvData_Raw[i++] = 0x02;  // Incomplete List of 16-bit Service UUIDs type
        AdvData_Raw[i++] = 0x80 + (rand() % 3) + 1;   // Service UUID (part of hex dump)
        AdvData_Raw[i++] = 0x30;

        AdvData_Raw[i++] = 0x02;  // TX Power level length
        AdvData_Raw[i++] = 0x0A;  // TX Power level type
        AdvData_Raw[i++] = 0x00;  // TX Power level value

        // Manufacturer specific data based on your hex dump
        AdvData_Raw[i++] = 0x05;  // Length of Manufacturer Specific Data section
        AdvData_Raw[i++] = 0xFF;  // Manufacturer Specific Data type
        AdvData_Raw[i++] = 0xBA;  // LSB of Manufacturer ID (Flipper Zero: 0x0FBA)
        AdvData_Raw[i++] = 0x0F;  // MSB of Manufacturer ID

        AdvData_Raw[i++] = 0x4C;  // Example data (remaining as in your dump)
        AdvData_Raw[i++] = 0x75;
        AdvData_Raw[i++] = 0x67;
        AdvData_Raw[i++] = 0x26;
        AdvData_Raw[i++] = 0xE1;
        AdvData_Raw[i++] = 0x80;

        // Add the constructed Advertisement Data to the BLE advertisement
        AdvData.addData(std::string((char *)AdvData_Raw, i));

        break;
      }

      case Airtag: {
        for (int i = 0; i < airtags->size(); i++) {
          if (airtags->get(i).selected) {
            AdvData.addData(std::string((char*)airtags->get(i).payload.data(), airtags->get(i).payloadSize));

            break;
          }
        }

        break;
      }
      default: {
        Serial.println("Please Provide a Company Type");
        break;
      }
    }

    delete[] AdvData_Raw;

    return AdvData;
  }
  //// https://github.com/Spooks4576


  class bluetoothScanAllCallback: public NimBLEAdvertisedDeviceCallbacks {
  
      void onResult(NimBLEAdvertisedDevice *advertisedDevice) {

        extern WiFiScan wifi_scan_obj;
  
        //#ifdef HAS_SCREEN
        //  int buf = display_obj.display_buffer->size();
        //#else
        int buf = 0;
        //#endif
          
        String display_string = "";

        if (wifi_scan_obj.currentScanMode == BT_SCAN_AIRTAG) {
          uint8_t* payLoad = advertisedDevice->getPayload();
          size_t len = advertisedDevice->getPayloadLength();

          bool match = false;
          for (int i = 0; i <= len - 4; i++) {
            if (payLoad[i] == 0x1E && payLoad[i+1] == 0xFF && payLoad[i+2] == 0x4C && payLoad[i+3] == 0x00) {
              match = true;
              break;
            }
            if (payLoad[i] == 0x4C && payLoad[i+1] == 0x00 && payLoad[i+2] == 0x12 && payLoad[i+3] == 0x19) {
              match = true;
              break;
            }
          }

          if (match) {
            String mac = advertisedDevice->getAddress().toString().c_str();
            mac.toUpperCase();

            for (int i = 0; i < airtags->size(); i++) {
              if (mac == airtags->get(i).mac)
                return;
            }

            int rssi = advertisedDevice->getRSSI();
            Serial.print("RSSI: ");
            Serial.print(rssi);
            Serial.print(" MAC: ");
            Serial.println(mac);
            Serial.print("Len: ");
            Serial.print(len);
            Serial.print(" Payload: ");
            for (size_t i = 0; i < len; i++) {
              Serial.printf("%02X ", payLoad[i]);
            }
            Serial.println("\n");

            AirTag airtag;
            airtag.mac = mac;
            airtag.payload.assign(payLoad, payLoad + len);
            airtag.payloadSize = len;

            airtags->add(airtag);


            #ifdef HAS_SCREEN
              //display_string.concat("RSSI: ");
              display_string.concat((String)rssi);
              display_string.concat(" MAC: ");
              display_string.concat(mac);
              uint8_t temp_len = display_string.length();
              for (uint8_t i = 0; i < 40 - temp_len; i++)
              {
                display_string.concat(" ");
              }
              display_obj.display_buffer->add(display_string);
            #endif
          }
        }
        else if (wifi_scan_obj.currentScanMode == BT_SCAN_FLIPPER) {
          uint8_t* payLoad = advertisedDevice->getPayload();
          size_t len = advertisedDevice->getPayloadLength();

          bool match = false;
          String color = "";
          for (int i = 0; i <= len - 4; i++) {
            if (payLoad[i] == 0x81 && payLoad[i+1] == 0x30) {
              match = true;
              color = "Black";
              break;
            }
            if (payLoad[i] == 0x82 && payLoad[i+1] == 0x30) {
              match = true;
              color = "White";
              break;
            }
            if (payLoad[i] == 0x83 && payLoad[i+1] == 0x30) {
              color = "Transparent";
              match = true;
              break;
            }
          }

          if (match) {
            String mac = advertisedDevice->getAddress().toString().c_str();
            String name = advertisedDevice->getName().c_str();
            mac.toUpperCase();

            for (int i = 0; i < flippers->size(); i++) {
              if (mac == flippers->get(i).mac)
                return;
            }

            int rssi = advertisedDevice->getRSSI();
            Serial.print("RSSI: ");
            Serial.print(rssi);
            Serial.print(" MAC: ");
            Serial.println(mac);
            Serial.print("Name: ");
            Serial.println(name);

            Flipper flipper;
            flipper.mac = mac;
            flipper.name = name;

            flippers->add(flipper);


            /*#ifdef HAS_SCREEN
              //display_string.concat("RSSI: ");
              display_string.concat((String)rssi);
              display_string.concat(" Flipper: ");
              display_string.concat(name);
              uint8_t temp_len = display_string.length();
              for (uint8_t i = 0; i < 40 - temp_len; i++)
              {
                display_string.concat(" ");
              }
              display_obj.display_buffer->add(display_string);
            #endif*/

            #ifdef HAS_SCREEN
              display_obj.display_buffer->add(String("Flipper: ") + name + ",                 ");
              display_obj.display_buffer->add("       MAC: " + String(mac) + ",             ");
              display_obj.display_buffer->add("      RSSI: " + String(rssi) + ",               ");
              display_obj.display_buffer->add("     Color: " + String(color) + "                ");
            #endif
          }
        }
        else if (wifi_scan_obj.currentScanMode == BT_SCAN_ALL) {
          if (buf >= 0)
          {
            display_string.concat(text_table4[0]);
            display_string.concat(advertisedDevice->getRSSI());
            Serial.print(" RSSI: ");
            Serial.print(advertisedDevice->getRSSI());
    
            display_string.concat(" ");
            Serial.print(" ");
            
            Serial.print("Device: ");
            if(advertisedDevice->getName().length() != 0)
            {
              display_string.concat(advertisedDevice->getName().c_str());
              Serial.print(advertisedDevice->getName().c_str());
              
            }
            else
            {
              display_string.concat(advertisedDevice->getAddress().toString().c_str());
              Serial.print(advertisedDevice->getAddress().toString().c_str());
            }
    
            #ifdef HAS_SCREEN
              uint8_t temp_len = display_string.length();
              for (uint8_t i = 0; i < 40 - temp_len; i++)
              {
                display_string.concat(" ");
              }
      
              Serial.println();
      
              while (display_obj.printing)
                delay(1);
              display_obj.loading = true;
              display_obj.display_buffer->add(display_string);
              display_obj.loading = false;
            #endif
          }
        }
        else if ((wifi_scan_obj.currentScanMode == BT_SCAN_WAR_DRIVE)  || (wifi_scan_obj.currentScanMode == BT_SCAN_WAR_DRIVE_CONT)) {
          #ifdef HAS_GPS
            if (gps_obj.getGpsModuleStatus()) {
              bool do_save = false;
              if (buf >= 0)
              {                
                Serial.print("Device: ");
                if(advertisedDevice->getName().length() != 0)
                {
                  display_string.concat(advertisedDevice->getName().c_str());
                  Serial.print(advertisedDevice->getName().c_str());
                  
                }
                else
                {
                  display_string.concat(advertisedDevice->getAddress().toString().c_str());
                  Serial.print(advertisedDevice->getAddress().toString().c_str());
                }

                if (gps_obj.getFixStatus()) {
                  do_save = true;
                  display_string.concat(" | Lt: " + gps_obj.getLat());
                  display_string.concat(" | Ln: " + gps_obj.getLon());
                }
                else {
                  display_string.concat(" | GPS: No Fix");
                }
        
                #ifdef HAS_SCREEN
                  uint8_t temp_len = display_string.length();
                  for (uint8_t i = 0; i < 40 - temp_len; i++)
                  {
                    display_string.concat(" ");
                  }
          
                  Serial.println();
          
                  while (display_obj.printing)
                    delay(1);
                  display_obj.loading = true;
                  display_obj.display_buffer->add(display_string);
                  display_obj.loading = false;
                #endif

                String wardrive_line = (String)advertisedDevice->getAddress().toString().c_str() + ",,[BLE]," + gps_obj.getDatetime() + ",0," + (String)advertisedDevice->getRSSI() + "," + gps_obj.getLat() + "," + gps_obj.getLon() + "," + gps_obj.getAlt() + "," + gps_obj.getAccuracy() + ",BLE\n";
                Serial.print(wardrive_line);

                if (do_save)
                  buffer_obj.append(wardrive_line);
              }
            }
          #endif
        }
        else if (wifi_scan_obj.currentScanMode == BT_SCAN_ANALYZER) {
          wifi_scan_obj._analyzer_value++;

          if (wifi_scan_obj.analyzer_frames_recvd < 254)
            wifi_scan_obj.analyzer_frames_recvd++;

          if (wifi_scan_obj.analyzer_frames_recvd > ANALYZER_NAME_REFRESH) {
            display_string.concat(advertisedDevice->getRSSI());
            display_string.concat(" ");

            if(advertisedDevice->getName().length() != 0)
              display_string.concat(advertisedDevice->getName().c_str());
            else
              display_string.concat(advertisedDevice->getAddress().toString().c_str());

            wifi_scan_obj.analyzer_frames_recvd = 0;
            wifi_scan_obj.analyzer_name_string = display_string;
            wifi_scan_obj.analyzer_name_update = true;
          }
        }
      }
  };
  
  class bluetoothScanSkimmersCallback: public BLEAdvertisedDeviceCallbacks {
      void onResult(BLEAdvertisedDevice *advertisedDevice) {
        String bad_list[bad_list_length] = {"HC-03", "HC-05", "HC-06"};
  
        #ifdef HAS_SCREEN
          int buf = display_obj.display_buffer->size();
        #else
          int buf = 0;
        #endif
          
        if (buf >= 0)
        {
          Serial.print("Device: ");
          String display_string = "";
          if(advertisedDevice->getName().length() != 0)
          {
            Serial.print(advertisedDevice->getName().c_str());
            for(uint8_t i = 0; i < bad_list_length; i++)
            {
              #ifdef HAS_SCREEN
                if(strcmp(advertisedDevice->getName().c_str(), bad_list[i].c_str()) == 0)
                {
                  display_string.concat(text_table4[1]);
                  display_string.concat(" ");
                  display_string.concat(advertisedDevice->getName().c_str());
                  uint8_t temp_len = display_string.length();
                  for (uint8_t i = 0; i < 40 - temp_len; i++)
                  {
                    display_string.concat(" ");
                  }
                  while (display_obj.printing)
                    delay(1);
                  display_obj.loading = true;
                  display_obj.display_buffer->add(display_string);
                  display_obj.loading = false;
                }
              #endif
            }
          }
          else
          {
            Serial.print(advertisedDevice->getAddress().toString().c_str());
          }
          Serial.print(" RSSI: ");
          Serial.println(advertisedDevice->getRSSI());
        }
      }
  };
#endif


WiFiScan::WiFiScan()
{
}

/*String WiFiScan::macToString(const Station& station) {
  char macStr[18]; // 6 pairs of hex digits + 5 colons + null terminator
  snprintf(macStr, sizeof(macStr), "%02X:%02X:%02X:%02X:%02X:%02X",
           station.mac[0], station.mac[1], station.mac[2],
           station.mac[3], station.mac[4], station.mac[5]);
  return String(macStr);
}*/

void WiFiScan::RunSetup() {
  if (my_ieee_check(31337, 0, 0) == 1)
    this->wsl_bypass_enabled = true;
  else
    this->wsl_bypass_enabled = false;

  #ifdef HAS_PSRAM
    ssids = new (ps_malloc(sizeof(LinkedList<ssid>))) LinkedList<ssid>();
    new (ssids) LinkedList<ssid>();
  #else
    ssids = new LinkedList<ssid>();
  #endif
  access_points = new LinkedList<AccessPoint>();
  airtags = new LinkedList<AirTag>();
  flippers = new LinkedList<Flipper>();
  ipList = new LinkedList<IPAddress>();
  probe_req_ssids = new LinkedList<ProbeReqSsid>;
  // for Pinescan
  pinescan_trackers = new LinkedList<PineScanTracker>();
  confirmed_pinescan = new LinkedList<ConfirmedPineScan>();
  pinescan_list_full_reported = false;
  // for MultiSSID
  multissid_trackers = new LinkedList<MultiSSIDTracker>();
  confirmed_multissid = new LinkedList<ConfirmedMultiSSID>();
  multissid_list_full_reported = false;

  #ifdef HAS_PSRAM
    mac_history = (struct mac_addr*) ps_malloc(mac_history_len * sizeof(struct mac_addr));
  #endif

  #ifdef HAS_BT
    watch_models = new WatchModel[26] {
      {0x1A, "Fallback Watch"},
      {0x01, "White Watch4 Classic 44m"},
      {0x02, "Black Watch4 Classic 40m"},
      {0x03, "White Watch4 Classic 40m"},
      {0x04, "Black Watch4 44mm"},
      {0x05, "Silver Watch4 44mm"},
      {0x06, "Green Watch4 44mm"},
      {0x07, "Black Watch4 40mm"},
      {0x08, "White Watch4 40mm"},
      {0x09, "Gold Watch4 40mm"},
      {0x0A, "French Watch4"},
      {0x0B, "French Watch4 Classic"},
      {0x0C, "Fox Watch5 44mm"},
      {0x11, "Black Watch5 44mm"},
      {0x12, "Sapphire Watch5 44mm"},
      {0x13, "Purpleish Watch5 40mm"},
      {0x14, "Gold Watch5 40mm"},
      {0x15, "Black Watch5 Pro 45mm"},
      {0x16, "Gray Watch5 Pro 45mm"},
      {0x17, "White Watch5 44mm"},
      {0x18, "White & Black Watch5"},
      {0x1B, "Black Watch6 Pink 40mm"},
      {0x1C, "Gold Watch6 Gold 40mm"},
      {0x1D, "Silver Watch6 Cyan 44mm"},
      {0x1E, "Black Watch6 Classic 43m"},
      {0x20, "Green Watch6 Classic 43m"},
    };
    
    NimBLEDevice::setScanFilterMode(CONFIG_BTDM_SCAN_DUPL_TYPE_DEVICE);
    NimBLEDevice::setScanDuplicateCacheSize(200);
    NimBLEDevice::init("");
    pBLEScan = NimBLEDevice::getScan(); //create new scan
    this->ble_initialized = true;
    
    this->shutdownBLE();
    esp_wifi_init(&cfg);
    #ifdef HAS_DUAL_BAND
      esp_wifi_set_country(&country);
      esp_event_loop_create_default();
    #endif
    esp_wifi_set_mode(WIFI_AP_STA);
    esp_wifi_start();
    this->wifi_initialized = true;
    esp_wifi_get_mac(WIFI_IF_STA, this->sta_mac);
    delay(10);
    esp_wifi_get_mac(WIFI_IF_AP, this->ap_mac);
    this->setMac();
    this->shutdownWiFi();
  #endif

  this->initWiFi(1);
}

bool WiFiScan::isHostAlive(IPAddress ip) {
  if (ip != IPAddress(0, 0, 0, 0))
    return Ping.ping(ip, 1);  // 1 try, returns true if reply received
  else
    return false;
}

int WiFiScan::clearStations() {
  int num_cleared = stations.size();
  stations.clear();
  Serial.println("stations: " + String(stations.size()));

  // Old versions had stations per AP; now global, so nothing else to clear.
  return num_cleared;
}


bool WiFiScan::checkMem() {
  if (esp_get_free_heap_size() <= MEM_LOWER_LIM)
    return false;
  else
    return true;
}

int WiFiScan::clearAPs() {
  int num_cleared = access_points->size();
  while (access_points->size() > 0)
    access_points->remove(0);
  Serial.println("access_points: " + (String)access_points->size());
  return num_cleared;
}

int WiFiScan::clearIPs() {
  int num_cleared = ipList->size();
  while (ipList->size() > 0)
    ipList->remove(0);
  Serial.println("ipList: " + (String)ipList->size());
  return num_cleared;
}

int WiFiScan::clearAirtags() {
  int num_cleared = airtags->size();
  while (airtags->size() > 0)
    airtags->remove(0);
  Serial.println("airtags: " + (String)airtags->size());
  return num_cleared;
}

int WiFiScan::clearFlippers() {
  int num_cleared = flippers->size();
  while (flippers->size() > 0)
    flippers->remove(0);
  Serial.println("Flippers: " + (String)flippers->size());
  return num_cleared;
}

int WiFiScan::clearSSIDs() {
  int num_cleared = ssids->size();
  ssids->clear();
  Serial.println("ssids: " + (String)ssids->size());
  return num_cleared;
}

bool WiFiScan::addSSID(String essid) {
  ssid s = {essid, random(1, 12), {random(256), random(256), random(256), random(256), random(256), random(256)}, false};
  ssids->add(s);
  Serial.println(ssids->get(ssids->size() - 1).essid);

  return true;
}

int WiFiScan::generateSSIDs(int count) {
  uint8_t num_gen = count;
  for (uint8_t x = 0; x < num_gen; x++) {
    String essid = "";

    for (uint8_t i = 0; i < 6; i++)
      essid.concat(alfa[random(65)]);

    ssid s = {essid, random(1, 12), {random(256), random(256), random(256), random(256), random(256), random(256)}, false};
    ssids->add(s);
    Serial.println(ssids->get(ssids->size() - 1).essid);
  }

  Serial.print("Free Heap: ");
  Serial.print(esp_get_free_heap_size());
  #ifdef HAS_PSRAM
    Serial.print(" Free PSRAM: ");
    Serial.println(heap_caps_get_free_size(MALLOC_CAP_SPIRAM));
  #endif

  return num_gen;
}

bool WiFiScan::joinWiFi(String ssid, String password, bool gui)
{
  static const char * btns[] ={text16, ""};
  int count = 0;
  
  if ((WiFi.status() == WL_CONNECTED) && (ssid == connected_network) && (ssid != "")) {
    #ifdef HAS_TOUCH
      if (gui) {
        lv_obj_t * mbox1 = lv_msgbox_create(lv_scr_act(), NULL);
        lv_msgbox_set_text(mbox1, text_table4[2]);
        lv_msgbox_add_btns(mbox1, btns);
        lv_obj_set_width(mbox1, 200);
        lv_obj_align(mbox1, NULL, LV_ALIGN_CENTER, 0, 0); //Align to the corner
      }
    #endif
    this->wifi_initialized = true;
    this->currentScanMode = WIFI_CONNECTED;
    return true;
  }
  else if (WiFi.status() == WL_CONNECTED) {
    Serial.println("Already connected. Disconnecting...");
    WiFi.disconnect();
  }

  WiFi.disconnect(true);
  delay(100);
  WiFi.mode(WIFI_MODE_STA);

  //esp_wifi_set_mode(WIFI_IF_STA);

  this->setMac();
    
  WiFi.begin(ssid.c_str(), password.c_str());

  #ifdef HAS_SCREEN
    #ifdef HAS_MINI_KB
      if (gui) {
        display_obj.clearScreen();
        display_obj.tft.setCursor(0, TFT_HEIGHT / 2);
        display_obj.tft.setTextSize(1);
        display_obj.tft.print("Connecting");
        display_obj.tft.setTextWrap(true, false);
      }
    #endif
  #endif

  Serial.print("Connecting to WiFi");
  while (WiFi.status() != WL_CONNECTED) {
    delay(500);
    Serial.print(".");
    #ifdef HAS_SCREEN
      #ifdef HAS_MINI_KB
        if (gui) {
          display_obj.tft.print(".");
        }
      #endif
    #endif
    count++;
    if (count == 20)
    {
      Serial.println("\nCould not connect to WiFi network");
      #ifdef HAS_SCREEN
        #ifdef HAS_MINI_KB
          if (gui) {
            display_obj.tft.println("\nFailed to connect");
            delay(1000);
          }
        #endif
      #endif
      #ifdef HAS_TOUCH
        if (gui) {
          lv_obj_t * mbox1 = lv_msgbox_create(lv_scr_act(), NULL);
          lv_msgbox_set_text(mbox1, text_table4[3]);
          lv_msgbox_add_btns(mbox1, btns);
          lv_obj_set_width(mbox1, 200);
          //lv_obj_set_event_cb(mbox1, event_handler);
          lv_obj_align(mbox1, NULL, LV_ALIGN_CENTER, 0, 0); //Align to the corner
        }
      #endif
      this->wifi_initialized = true;
      this->StartScan(WIFI_SCAN_OFF, TFT_BLACK);
      #ifdef HAS_SCREEN
        display_obj.tft.setTextWrap(false, false);
      #endif
      return false;
    }
  }
  
  #ifdef HAS_TOUCH
    lv_obj_t * mbox1 = lv_msgbox_create(lv_scr_act(), NULL);
    lv_msgbox_set_text(mbox1, text_table4[4]);
    lv_msgbox_add_btns(mbox1, btns);
    lv_obj_set_width(mbox1, 200);
    lv_obj_align(mbox1, NULL, LV_ALIGN_CENTER, 0, 0); //Align to the corner
  #endif
  this->connected_network = ssid;
  this->ip_addr = WiFi.localIP();
  this->gateway = WiFi.gatewayIP();
  this->subnet = WiFi.subnetMask();
  
  Serial.println("\nConnected to the WiFi network");
  Serial.print("IP address: ");
  Serial.println(this->ip_addr);
  Serial.print("Gateway: ");
  Serial.println(this->gateway);
  Serial.print("Netmask: ");
  Serial.println(this->subnet);
  Serial.print("MAC: ");
  Serial.println(WiFi.macAddress());

  #ifdef HAS_SCREEN
    #ifdef HAS_MINI_KB
      display_obj.tft.println("\nConnected!");
      display_obj.tft.print("IP address: ");
      display_obj.tft.println(this->ip_addr);
      display_obj.tft.print("Gateway: ");
      display_obj.tft.println(this->gateway);
      display_obj.tft.print("Netmask: ");
      display_obj.tft.println(this->subnet);
      display_obj.tft.print("MAC: ");
      display_obj.tft.println(WiFi.macAddress());
      display_obj.tft.println("Returning...");
      delay(2000);
    #endif
  #endif
  this->wifi_initialized = true;
  #ifndef HAS_TOUCH
    this->currentScanMode = WIFI_CONNECTED;
    #ifdef HAS_SCREEN
      display_obj.tft.setTextWrap(false, false);
    #endif
  #endif

  settings_obj.saveSetting<bool>("ClientSSID", ssid);
  settings_obj.saveSetting<bool>("ClientPW", password);

  return true;
}

bool WiFiScan::startWiFi(String ssid, String password, bool gui)
{
  static const char * btns[] ={text16, ""};
  int count = 0;
  
  if ((WiFi.status() == WL_CONNECTED) && (ssid == connected_network) && (ssid != "")) {
    #ifdef HAS_TOUCH
      if (gui) {
        lv_obj_t * mbox1 = lv_msgbox_create(lv_scr_act(), NULL);
        lv_msgbox_set_text(mbox1, text_table4[2]);
        lv_msgbox_add_btns(mbox1, btns);
        lv_obj_set_width(mbox1, 200);
        lv_obj_align(mbox1, NULL, LV_ALIGN_CENTER, 0, 0); //Align to the corner
      }
    #endif
    this->wifi_initialized = true;
    this->currentScanMode = WIFI_CONNECTED;
    return true;
  }
  else if (WiFi.status() == WL_CONNECTED) {
    Serial.println("Already connected. Disconnecting...");
    WiFi.disconnect();
  }

  WiFi.disconnect(true);
  delay(100);
  WiFi.mode(WIFI_MODE_AP);

  //esp_wifi_set_mode(WIFI_IF_STA);

  this->setMac();
    
  if (password != "")
    WiFi.softAP(ssid.c_str(), password.c_str());
  else
    WiFi.softAP(ssid.c_str());

  #ifdef HAS_SCREEN
    #ifdef HAS_MINI_KB
      if (gui) {
        display_obj.clearScreen();
        display_obj.tft.setCursor(0, TFT_HEIGHT / 2);
        display_obj.tft.setTextSize(1);
        display_obj.tft.print("Starting");
        display_obj.tft.setTextWrap(true, false);
      }
    #endif
  #endif

  Serial.print("Started WiFi");
  
  #ifdef HAS_TOUCH
    lv_obj_t * mbox1 = lv_msgbox_create(lv_scr_act(), NULL);
    lv_msgbox_set_text(mbox1, text_table4[4]);
    lv_msgbox_add_btns(mbox1, btns);
    lv_obj_set_width(mbox1, 200);
    lv_obj_align(mbox1, NULL, LV_ALIGN_CENTER, 0, 0); //Align to the corner
  #endif
  this->connected_network = ssid;
  this->ip_addr = WiFi.softAPIP();
  this->gateway = WiFi.gatewayIP();
  this->subnet = WiFi.subnetMask();
  
  Serial.println("\nStarted AP");
  Serial.print("IP address: ");
  Serial.println(this->ip_addr);
  Serial.print("Gateway: ");
  Serial.println(this->gateway);
  Serial.print("Netmask: ");
  Serial.println(this->subnet);
  Serial.print("MAC: ");
  Serial.println(WiFi.macAddress());

  #ifdef HAS_SCREEN
    #ifdef HAS_MINI_KB
      display_obj.tft.println("\nStarted AP");
      display_obj.tft.print("IP address: ");
      display_obj.tft.println(this->ip_addr);
      display_obj.tft.print("Gateway: ");
      display_obj.tft.println(this->gateway);
      display_obj.tft.print("Netmask: ");
      display_obj.tft.println(this->subnet);
      display_obj.tft.print("MAC: ");
      display_obj.tft.println(WiFi.macAddress());
      display_obj.tft.println("Returning...");
      delay(2000);
    #endif
  #endif
  this->wifi_initialized = true;
  #ifndef HAS_TOUCH
    this->currentScanMode = WIFI_CONNECTED;
    #ifdef HAS_SCREEN
      display_obj.tft.setTextWrap(false, false);
    #endif
  #endif

  //settings_obj.saveSetting<bool>("APSSID", ssid);
  //settings_obj.saveSetting<bool>("APPW", password);

  return true;
}

// Apply WiFi settings
void WiFiScan::initWiFi(uint8_t scan_mode) {
  // Set the channel
  if (scan_mode != WIFI_SCAN_OFF) {
    //Serial.println(F("Initializing WiFi settings..."));
    this->changeChannel();
  
    this->force_pmkid = settings_obj.loadSetting<bool>(text_table4[5]);
    this->force_probe = settings_obj.loadSetting<bool>(text_table4[6]);
    this->save_pcap = settings_obj.loadSetting<bool>(text_table4[7]);
    this->ep_deauth = settings_obj.loadSetting<bool>("EPDeauth");
    settings_obj.loadSetting<String>("ClientSSID");
    settings_obj.loadSetting<String>("ClientPW");
    //Serial.println(F("Initialization complete"));
  }
}

bool WiFiScan::scanning() {
  if (this->currentScanMode == WIFI_SCAN_OFF)
    return false;
  else
    return true;
}

// Function to prepare to run a specific scan
void WiFiScan::StartScan(uint8_t scan_mode, uint16_t color)
{  
  this->initWiFi(scan_mode);
  if (scan_mode == WIFI_SCAN_OFF)
    StopScan(scan_mode);
  else if (scan_mode == WIFI_SCAN_PROBE)
    RunProbeScan(scan_mode, color);
  else if (scan_mode == WIFI_SCAN_STATION_WAR_DRIVE)
    RunProbeScan(scan_mode, color);
  else if (scan_mode == WIFI_SCAN_EVIL_PORTAL)
    RunEvilPortal(scan_mode, color);
  else if (scan_mode == WIFI_SCAN_EAPOL)
    RunEapolScan(scan_mode, color);
  else if (scan_mode == WIFI_SCAN_ACTIVE_EAPOL)
    RunEapolScan(scan_mode, color);
  else if (scan_mode == WIFI_SCAN_ACTIVE_LIST_EAPOL)
    RunEapolScan(scan_mode, color);
  else if (scan_mode == WIFI_SCAN_AP)
    RunBeaconScan(scan_mode, color);
  else if (scan_mode == WIFI_SCAN_WAR_DRIVE)
    RunBeaconScan(scan_mode, color);
  else if (scan_mode == WIFI_SCAN_SIG_STREN)
    RunRawScan(scan_mode, color);    
  else if (scan_mode == WIFI_SCAN_RAW_CAPTURE)
    RunRawScan(scan_mode, color);
  else if (scan_mode == WIFI_SCAN_STATION)
    RunStationScan(scan_mode, color);
  else if (scan_mode == WIFI_SCAN_TARGET_AP)
    RunAPScan(scan_mode, color);
  else if (scan_mode == WIFI_SCAN_TARGET_AP_FULL)
    RunAPScan(scan_mode, color);
  else if (scan_mode == WIFI_SCAN_AP_STA)
    RunAPScan(scan_mode, color);
  else if (scan_mode == WIFI_SCAN_PWN)
    RunPwnScan(scan_mode, color);
  else if (scan_mode == WIFI_SCAN_PINESCAN)
    RunPineScan(scan_mode, color);
  else if (scan_mode == WIFI_SCAN_MULTISSID)
    RunMultiSSIDScan(scan_mode, color);
  else if (scan_mode == WIFI_SCAN_DEAUTH)
    RunDeauthScan(scan_mode, color);
  else if (scan_mode == WIFI_PACKET_MONITOR) {
    #ifdef HAS_SCREEN
      RunPacketMonitor(scan_mode, color);
    #endif
  }
  else if ((scan_mode == WIFI_SCAN_CHAN_ANALYZER) ||
          (scan_mode == WIFI_SCAN_PACKET_RATE)) {
    //#ifdef HAS_SCREEN
      RunPacketMonitor(scan_mode, color);
    //#endif
  }
  else if (scan_mode == WIFI_ATTACK_BEACON_LIST)
    this->startWiFiAttacks(scan_mode, color, text_table1[50]);
  else if (scan_mode == WIFI_ATTACK_BEACON_SPAM)
    this->startWiFiAttacks(scan_mode, color, text_table1[51]);
  else if (scan_mode == WIFI_ATTACK_RICK_ROLL)
    this->startWiFiAttacks(scan_mode, color, text_table1[52]);
  else if (scan_mode == WIFI_ATTACK_FUNNY_BEACON)
    this->startWiFiAttacks(scan_mode, color, text1_67);
  else if (scan_mode == WIFI_ATTACK_AUTH)
    this->startWiFiAttacks(scan_mode, color, text_table1[53]);
  else if (scan_mode == WIFI_ATTACK_DEAUTH)
    this->startWiFiAttacks(scan_mode, color, text_table4[8]);
  else if (scan_mode == WIFI_ATTACK_DEAUTH_MANUAL)
    this->startWiFiAttacks(scan_mode, color, text_table4[8]);
  else if (scan_mode == WIFI_ATTACK_DEAUTH_TARGETED)
    this->startWiFiAttacks(scan_mode, color, text_table4[47]);
  else if (scan_mode == WIFI_ATTACK_BAD_MSG_TARGETED)
    this->startWiFiAttacks(scan_mode, color, "Bad Msg Targ");
  else if (scan_mode == WIFI_ATTACK_BAD_MSG)
    this->startWiFiAttacks(scan_mode, color, "Bad Msg");
  else if (scan_mode == WIFI_ATTACK_SLEEP)
    this->startWiFiAttacks(scan_mode, color, "Sleep");
  else if (scan_mode == WIFI_ATTACK_SLEEP_TARGETED)
    this->startWiFiAttacks(scan_mode, color, "Sleep Targeted");
  else if (scan_mode == WIFI_ATTACK_AP_SPAM)
    this->startWiFiAttacks(scan_mode, color, " AP Beacon Spam ");
  else if ((scan_mode == BT_SCAN_ALL) || (scan_mode == BT_SCAN_AIRTAG) || (scan_mode == BT_SCAN_FLIPPER) || (scan_mode == BT_SCAN_ANALYZER)){
    #ifdef HAS_BT
      RunBluetoothScan(scan_mode, color);
    #endif
  }
  else if (scan_mode == BT_ATTACK_SOUR_APPLE) {
    #ifdef HAS_BT
      RunSourApple(scan_mode, color);
    #endif
  }
  else if ((scan_mode == BT_ATTACK_SWIFTPAIR_SPAM) || 
           (scan_mode == BT_ATTACK_SPAM_ALL) ||
           (scan_mode == BT_ATTACK_SAMSUNG_SPAM) ||
           (scan_mode == BT_ATTACK_GOOGLE_SPAM) ||
           (scan_mode == BT_ATTACK_FLIPPER_SPAM) ||
           (scan_mode == BT_SPOOF_AIRTAG)) {
    #ifdef HAS_BT
      RunSwiftpairSpam(scan_mode, color);
    #endif
  }
  else if ((scan_mode == BT_SCAN_WAR_DRIVE) ||
           (scan_mode == BT_SCAN_WAR_DRIVE_CONT)) {
    #ifdef HAS_BT
      RunBluetoothScan(scan_mode, color);
    #endif
  }
  else if (scan_mode == BT_SCAN_SKIMMERS) {
    #ifdef HAS_BT
      RunBluetoothScan(scan_mode, color);
    #endif
  }
  else if (scan_mode == LV_ADD_SSID) {
    #ifdef HAS_SCREEN
      RunLvJoinWiFi(scan_mode, color);
    #endif
  }
  else if (scan_mode == LV_JOIN_WIFI) {
    #ifdef HAS_SCREEN
      RunLvJoinWiFi(scan_mode, color);
    #endif
  }
  else if (scan_mode == WIFI_SCAN_GPS_NMEA){
    #ifdef HAS_GPS
      gps_obj.enable_queue();
    #endif
  }
  else if (scan_mode == GPS_TRACKER) {
    RunSetupGPSTracker(scan_mode);
  }
  else if (scan_mode == GPS_POI) {
    RunSetupGPSTracker(scan_mode);
  }
  else if (scan_mode == WIFI_PING_SCAN)
    RunPingScan(scan_mode, color);
  else if (scan_mode == WIFI_ARP_SCAN)
    RunPingScan(scan_mode, color);
  else if (scan_mode == WIFI_PORT_SCAN_ALL)
    RunPortScanAll(scan_mode, color);
  else if (scan_mode == WIFI_SCAN_SSH)
    RunPortScanAll(scan_mode, color);
  else if (scan_mode == WIFI_SCAN_TELNET)
    RunPortScanAll(scan_mode, color);
  else if (scan_mode == WIFI_SCAN_SMTP)
    RunPortScanAll(scan_mode, color);
  else if (scan_mode == WIFI_SCAN_DNS)
    RunPortScanAll(scan_mode, color);
  else if (scan_mode == WIFI_SCAN_HTTP)
    RunPortScanAll(scan_mode, color);
  else if (scan_mode == WIFI_SCAN_HTTPS)
    RunPortScanAll(scan_mode, color);
  else if (scan_mode == WIFI_SCAN_RDP)
    RunPortScanAll(scan_mode, color);

  this->currentScanMode = scan_mode;
}

void WiFiScan::startWiFiAttacks(uint8_t scan_mode, uint16_t color, String title_string) {
  // Common wifi attack configurations
  #ifdef HAS_SCREEN
    display_obj.TOP_FIXED_AREA_2 = 48;
    display_obj.tteBar = true;
    display_obj.print_delay_1 = 15;
    display_obj.print_delay_2 = 10;
    display_obj.initScrollValues(true);
    display_obj.tft.setTextWrap(false);
    display_obj.tft.setTextColor(TFT_BLACK, color);
    #ifdef HAS_FULL_SCREEN
      display_obj.tft.fillRect(0,16,TFT_WIDTH,16, color);
      display_obj.tft.drawCentreString((String)title_string,TFT_WIDTH / 2,16,2);
    #endif
    #ifdef HAS_ILI9341
      display_obj.touchToExit();
    #endif
    display_obj.tft.setTextColor(TFT_GREEN, TFT_BLACK);
  #endif

  //wifi_ap_config_t ap_config;
  //ap_config.ssid_hidden = 1;

  ap_config.ap.ssid_hidden = 1;
  ap_config.ap.beacon_interval = 10000;
  ap_config.ap.ssid_len = 0;
        
  packets_sent = 0;
  esp_wifi_init(&cfg);
  #ifdef HAS_DUAL_BAND
    esp_wifi_set_country(&country);
  #endif
  esp_wifi_set_storage(WIFI_STORAGE_RAM);
  esp_wifi_set_mode(WIFI_MODE_AP);
  esp_wifi_set_config(WIFI_IF_AP, &ap_config);
  esp_wifi_start();
  this->setMac();
  esp_wifi_set_channel(set_channel, WIFI_SECOND_CHAN_NONE);
  
  //WiFi.mode(WIFI_AP_STA);
  
  //esp_wifi_init(&cfg);
  //esp_wifi_set_storage(WIFI_STORAGE_RAM);
  //esp_wifi_set_mode(WIFI_AP_STA);
  //esp_wifi_start();
  //esp_wifi_set_promiscuous_filter(NULL);
  esp_wifi_set_promiscuous(true);
  esp_wifi_set_max_tx_power(82);
  this->wifi_initialized = true;
  #ifdef HAS_FLIPPER_LED
    flipper_led.attackLED();
  #elif defined(XIAO_ESP32_S3)
    xiao_led.attackLED();
  #elif defined(MARAUDER_M5STICKC)
    stickc_led.attackLED();
  #else
    led_obj.setMode(MODE_ATTACK);
  #endif
  initTime = millis();
}

bool WiFiScan::shutdownWiFi() {
  if (this->wifi_initialized) {
    if (!this->wifi_connected) {
      esp_wifi_set_promiscuous(false);
      WiFi.disconnect();
      WiFi.mode(WIFI_OFF);

      dst_mac = "ff:ff:ff:ff:ff:ff";
    
      esp_wifi_set_mode(WIFI_MODE_NULL);
      esp_wifi_stop();
      esp_wifi_restore();
      esp_wifi_deinit();
      esp_netif_deinit(); 
    }

    #ifdef HAS_FLIPPER_LED
      flipper_led.offLED();
    #elif defined(XIAO_ESP32_S3)
      xiao_led.offLED();
    #elif defined(MARAUDER_M5STICKC)
      stickc_led.offLED();
    #else
      led_obj.setMode(MODE_OFF);
    #endif

    this->_analyzer_value = 0;
  
    if (!this->wifi_connected)
      this->wifi_initialized = false;

    return true;
  }
  else {
    return false;
  }
}

bool WiFiScan::shutdownBLE() {
  #ifdef HAS_BT
    if (this->ble_initialized) {
      Serial.println("Shutting down BLE");
      pAdvertising->stop();
      pBLEScan->stop();
      
      pBLEScan->clearResults();
      NimBLEDevice::deinit();

      this->_analyzer_value = 0;
    
      this->ble_initialized = false;
    }
    else {
      return false;
    }

    #ifdef HAS_FLIPPER_LED
      flipper_led.offLED();
    #elif defined(XIAO_ESP32_S3)
      xiao_led.offLED();
    #elif defined(MARAUDER_M5STICKC)
      stickc_led.offLED();
    #else
      led_obj.setMode(MODE_OFF);
    #endif

  #endif

  return true;
}

// Pinescan cleanup
int WiFiScan::clearPineScanTrackers() {
  int num_cleared = pinescan_trackers->size() + confirmed_pinescan->size();
  pinescan_trackers->clear();
  confirmed_pinescan->clear();
  pinescan_list_full_reported = false;
  return num_cleared;
}

// MultiSSID Cleanup
int WiFiScan::clearMultiSSID() {
  int num_cleared = multissid_trackers->size() + confirmed_multissid->size();
  multissid_trackers->clear();
  confirmed_multissid->clear();
  multissid_list_full_reported = false;
  return num_cleared;
}

// Function to stop all wifi scans
void WiFiScan::StopScan(uint8_t scan_mode)
{
  if ((currentScanMode == WIFI_SCAN_PROBE) ||
  (currentScanMode == WIFI_SCAN_AP) ||
  (currentScanMode == WIFI_SCAN_WAR_DRIVE) ||
  (currentScanMode == WIFI_SCAN_STATION_WAR_DRIVE) ||
  (currentScanMode == WIFI_SCAN_EVIL_PORTAL) ||
  (currentScanMode == WIFI_SCAN_RAW_CAPTURE) ||
  (currentScanMode == WIFI_SCAN_STATION) ||
  (currentScanMode == WIFI_SCAN_SIG_STREN) ||
  (currentScanMode == WIFI_SCAN_TARGET_AP) ||
  (currentScanMode == WIFI_SCAN_TARGET_AP_FULL) ||
  (currentScanMode == WIFI_SCAN_AP_STA) ||
  (currentScanMode == WIFI_PING_SCAN) ||
  (currentScanMode == WIFI_ARP_SCAN) ||
  (currentScanMode == WIFI_PORT_SCAN_ALL) ||
  (currentScanMode == WIFI_SCAN_SSH) ||
  (currentScanMode == WIFI_SCAN_TELNET) ||
  (currentScanMode == WIFI_SCAN_SMTP) ||
  (currentScanMode == WIFI_SCAN_DNS) ||
  (currentScanMode == WIFI_SCAN_HTTP) ||
  (currentScanMode == WIFI_SCAN_HTTPS) ||
  (currentScanMode == WIFI_SCAN_RDP) ||
  (currentScanMode == WIFI_SCAN_PWN) ||
  (currentScanMode == WIFI_SCAN_PINESCAN) ||
  (currentScanMode == WIFI_SCAN_MULTISSID) ||
  (currentScanMode == WIFI_SCAN_EAPOL) ||
  (currentScanMode == WIFI_SCAN_ACTIVE_EAPOL) ||
  (currentScanMode == WIFI_SCAN_ACTIVE_LIST_EAPOL) ||
  (currentScanMode == WIFI_SCAN_ALL) ||
  (currentScanMode == WIFI_SCAN_DEAUTH) ||
  (currentScanMode == WIFI_ATTACK_BEACON_LIST) ||
  (currentScanMode == WIFI_ATTACK_BEACON_SPAM) ||
  (currentScanMode == WIFI_ATTACK_AUTH) ||
  (currentScanMode == WIFI_ATTACK_DEAUTH) ||
  (currentScanMode == WIFI_ATTACK_DEAUTH_MANUAL) ||
  (currentScanMode == WIFI_ATTACK_DEAUTH_TARGETED) ||
  (currentScanMode == WIFI_ATTACK_BAD_MSG_TARGETED) ||
  (currentScanMode == WIFI_ATTACK_BAD_MSG) ||
  (currentScanMode == WIFI_ATTACK_SLEEP) ||
  (currentScanMode == WIFI_ATTACK_SLEEP_TARGETED) ||
  (currentScanMode == WIFI_ATTACK_MIMIC) ||
  (currentScanMode == WIFI_ATTACK_RICK_ROLL) ||
  (currentScanMode == WIFI_ATTACK_FUNNY_BEACON) ||
  (currentScanMode == WIFI_PACKET_MONITOR) ||
  (currentScanMode == WIFI_SCAN_CHAN_ANALYZER) ||
  (currentScanMode == WIFI_SCAN_PACKET_RATE) ||
  (currentScanMode == WIFI_CONNECTED) ||
  (currentScanMode == LV_JOIN_WIFI) ||
  (this->wifi_initialized))
  {
    this->shutdownWiFi();

    if (!this->wifi_connected) {
      this->connected_network = "";
      this->ip_addr = IPAddress(0, 0, 0, 0);
      this->gateway = IPAddress(0, 0, 0, 0);
      this->subnet = IPAddress(0, 0, 0, 0);
    }

    #ifdef HAS_SCREEN
      for (int i = 0; i < TFT_WIDTH; i++) {
        this->_analyzer_values[i] = 0;
      }
      this->analyzer_name_string = "";
      this->analyzer_name_update = true;
      this->mgmt_frames = 0;
      this->data_frames = 0;
      this->beacon_frames = 0;
      this->req_frames = 0;
      this->resp_frames = 0;
      this->deauth_frames = 0;
      this->eapol_frames = 0;
      this->min_rssi = 0;
      this->max_rssi = -128;

      evil_portal_obj.cleanup();
    #endif
    evil_portal_obj.has_ap = false;
  }

  else if ((currentScanMode == GPS_TRACKER) ||
          (currentScanMode == GPS_POI)) {
    this->writeFooter(currentScanMode == GPS_POI);
  }

  
  else if ((currentScanMode == BT_SCAN_ALL) ||
  (currentScanMode == BT_SCAN_AIRTAG) ||
  (currentScanMode == BT_SCAN_FLIPPER) ||
  (currentScanMode == BT_ATTACK_SOUR_APPLE) ||
  (currentScanMode == BT_ATTACK_SWIFTPAIR_SPAM) ||
  (currentScanMode == BT_ATTACK_SPAM_ALL) ||
  (currentScanMode == BT_ATTACK_SAMSUNG_SPAM) ||
  (currentScanMode == BT_ATTACK_GOOGLE_SPAM) ||
  (currentScanMode == BT_ATTACK_FLIPPER_SPAM) ||
  (currentScanMode == BT_SPOOF_AIRTAG) ||
  (currentScanMode == BT_SCAN_WAR_DRIVE) ||
  (currentScanMode == BT_SCAN_WAR_DRIVE_CONT) ||
  (currentScanMode == BT_SCAN_SKIMMERS) ||
  (currentScanMode == BT_SCAN_ANALYZER))
  {
    #ifdef HAS_BT
      #ifdef HAS_SCREEN
        for (int i = 0; i < TFT_WIDTH; i++) {
          this->_analyzer_values[i] = 0;
        }
        this->analyzer_name_string = "";
        this->analyzer_name_update = true;
      #endif

      this->shutdownBLE();
    #endif
  }

  #ifdef HAS_SCREEN
    display_obj.display_buffer->clear();
    #ifdef SCREEN_BUFFER
      display_obj.screen_buffer->clear();
    #endif
    //Serial.print("display_buffer->size(): ");
    Serial.println(display_obj.display_buffer->size());
  
    display_obj.tteBar = false;
  #endif

  #ifdef HAS_GPS
    gps_obj.disable_queue();
  #endif
}

String WiFiScan::getStaMAC()
{
  char *buf;
  uint8_t mac[6];
  char macAddrChr[18] = {0};
  esp_wifi_init(&cfg2);
  #ifdef HAS_DUAL_BAND
    esp_wifi_set_country(&country);
  #endif
  esp_wifi_set_storage(WIFI_STORAGE_RAM);
  esp_wifi_set_mode(WIFI_MODE_STA);
  esp_wifi_start();
  this->setMac();
  esp_err_t mac_status = esp_wifi_get_mac(WIFI_IF_STA, mac);
  this->wifi_initialized = true;
  sprintf(macAddrChr, 
          "%02X:%02X:%02X:%02X:%02X:%02X",
          mac[0],
          mac[1],
          mac[2],
          mac[3],
          mac[4],
          mac[5]);
  this->shutdownWiFi();
  return String(macAddrChr);
}

String WiFiScan::getApMAC()
{
  char *buf;
  uint8_t mac[6];
  char macAddrChr[18] = {0};
  esp_wifi_init(&cfg2);
  #ifdef HAS_DUAL_BAND
    esp_wifi_set_country(&country);
  #endif
  esp_wifi_set_storage(WIFI_STORAGE_RAM);
  esp_wifi_set_mode(WIFI_MODE_AP);
  esp_wifi_start();
  this->setMac();
  esp_err_t mac_status = esp_wifi_get_mac(WIFI_IF_AP, mac);
  this->wifi_initialized = true;
  sprintf(macAddrChr, 
          "%02X:%02X:%02X:%02X:%02X:%02X",
          mac[0],
          mac[1],
          mac[2],
          mac[3],
          mac[4],
          mac[5]);
  this->shutdownWiFi();
  return String(macAddrChr);
}

bool WiFiScan::mac_cmp(struct mac_addr addr1, struct mac_addr addr2) {
  //Return true if 2 mac_addr structs are equal.
  for (int y = 0; y < 6 ; y++) {
    if (addr1.bytes[y] != addr2.bytes[y]) {
      return false;
    }
  }
  return true;
}

bool WiFiScan::seen_mac(unsigned char* mac) {
  //Return true if this MAC address is in the recently seen array.

  struct mac_addr tmp;
  for (int x = 0; x < 6 ; x++) {
    tmp.bytes[x] = mac[x];
  }

  for (int x = 0; x < mac_history_len; x++) {
    if (this->mac_cmp(tmp, mac_history[x])) {
      return true;
    }
  }
  return false;
}

void WiFiScan::save_mac(unsigned char* mac) {
  //Save a MAC address into the recently seen array.
  if (this->mac_history_cursor >= mac_history_len) {
    this->mac_history_cursor = 0;
  }
  struct mac_addr tmp;
  for (int x = 0; x < 6 ; x++) {
    tmp.bytes[x] = mac[x];
  }

  mac_history[this->mac_history_cursor] = tmp;
  this->mac_history_cursor++;
}

String WiFiScan::security_int_to_string(int security_type) {
  //Provide a security type int from WiFi.encryptionType(i) to convert it to a String which Wigle CSV expects.
  String authtype = "";

  switch (security_type) {
    case WIFI_AUTH_OPEN:
      authtype = "[OPEN]";
      break;
  
    case WIFI_AUTH_WEP:
      authtype = "[WEP]";
      break;
  
    case WIFI_AUTH_WPA_PSK:
      authtype = "[WPA_PSK]";
      break;
  
    case WIFI_AUTH_WPA2_PSK:
      authtype = "[WPA2_PSK]";
      break;
  
    case WIFI_AUTH_WPA_WPA2_PSK:
      authtype = "[WPA_WPA2_PSK]";
      break;
  
    case WIFI_AUTH_WPA2_ENTERPRISE:
      authtype = "[WPA2]";
      break;

    //Requires at least v2.0.0 of https://github.com/espressif/arduino-esp32/
    case WIFI_AUTH_WPA3_PSK:
      authtype = "[WPA3_PSK]";
      break;

    case WIFI_AUTH_WPA2_WPA3_PSK:
      authtype = "[WPA2_WPA3_PSK]";
      break;

    case WIFI_AUTH_WAPI_PSK:
      authtype = "[WAPI_PSK]";
      break;
        
    default:
      authtype = "[UNDEFINED]";
  }

  return authtype;
}

void WiFiScan::clearMacHistory() {
    for (int i = 0; i < mac_history_len; ++i) {
        memset(mac_history[i].bytes, 0, sizeof(mac_history[i].bytes));
    }
}

String WiFiScan::freeRAM()
{
  char s[150];
  sprintf(s, "RAM Free: %u bytes", esp_get_free_heap_size());
  this->free_ram = String(esp_get_free_heap_size());
  return String(s);
}

void WiFiScan::startPcap(String file_name) {
  buffer_obj.pcapOpen(
    file_name,
    #if defined(HAS_SD)
      sd_obj.supported ? &SD :
    #endif
    NULL,
    save_serial // Set with commandline options
  );
}

void WiFiScan::startLog(String file_name) {
  buffer_obj.logOpen(
    file_name,
    #if defined(HAS_SD)
      sd_obj.supported ? &SD :
    #endif
    NULL,
    save_serial // Set with commandline options
  );
}

void WiFiScan::startGPX(String file_name) {
  buffer_obj.gpxOpen(
    file_name,
    #if defined(HAS_SD)
      sd_obj.supported ? &SD :
    #endif
    NULL,
    save_serial // Set with commandline options
  );
}

void WiFiScan::parseBSSID(const char* bssidStr, uint8_t* bssid) {
  sscanf(bssidStr, "%02X:%02X:%02X:%02X:%02X:%02X",
         &bssid[0], &bssid[1], &bssid[2],
         &bssid[3], &bssid[4], &bssid[5]);
}

void WiFiScan::RunPingScan(uint8_t scan_mode, uint16_t color)
{
  if (scan_mode == WIFI_PING_SCAN)
    startLog("pingscan");
  else if (scan_mode == WIFI_ARP_SCAN)
    startLog("arpscan");

  #ifdef HAS_FLIPPER_LED
    flipper_led.sniffLED();
  #elif defined(XIAO_ESP32_S3)
    xiao_led.sniffLED();
  #elif defined(MARAUDER_M5STICKC)
    stickc_led.sniffLED();
  #else
    led_obj.setMode(MODE_SNIFF);
  #endif
  
  #ifdef HAS_SCREEN
    display_obj.TOP_FIXED_AREA_2 = 48;
    display_obj.tteBar = true;
    display_obj.print_delay_1 = 15;
    display_obj.print_delay_2 = 10;
    display_obj.initScrollValues(true);
    display_obj.tft.setTextWrap(false);
    display_obj.tft.setTextColor(TFT_BLACK, color);
    #ifdef HAS_FULL_SCREEN
      display_obj.tft.fillRect(0,16,TFT_WIDTH,16, color);
      if (scan_mode == WIFI_PING_SCAN)
        display_obj.tft.drawCentreString("Ping Scan",TFT_WIDTH / 2,16,2);
      else if (scan_mode == WIFI_ARP_SCAN)
        display_obj.tft.drawCentreString("ARP Scan",TFT_WIDTH / 2,16,2);
    #endif
    #ifdef HAS_ILI9341
      display_obj.touchToExit();
    #endif
    display_obj.tft.setTextColor(TFT_RED, TFT_BLACK);
    display_obj.setupScrollArea(display_obj.TOP_FIXED_AREA_2, BOT_FIXED_AREA);
  #endif
  this->current_scan_ip = this->gateway;
  Serial.println("Cleared IPs: " + (String)this->clearIPs());
  if (scan_mode == WIFI_PING_SCAN)
    Serial.println("Starting Ping Scan with...");
  else if (scan_mode == WIFI_ARP_SCAN)
    Serial.println("Starting ARP Scan with...");
  Serial.print("IP address: ");
  Serial.println(this->ip_addr);
  Serial.print("Gateway: ");
  Serial.println(this->gateway);
  Serial.print("Netmask: ");
  Serial.println(this->subnet);
  Serial.print("MAC: ");
  Serial.println(WiFi.macAddress());

  if (scan_mode == WIFI_PING_SCAN)
    buffer_obj.append("Starting Ping Scan with...");
  else if (scan_mode == WIFI_ARP_SCAN)
  buffer_obj.append("\nSSID: " + (String)this->connected_network);
  buffer_obj.append("\nIP address: ");
  buffer_obj.append(this->ip_addr.toString());
  buffer_obj.append("\nGateway: ");
  buffer_obj.append(this->gateway.toString());
  buffer_obj.append("\nNetmask: ");
  buffer_obj.append(this->subnet.toString());
  buffer_obj.append("\nMAC: ");
  buffer_obj.append((String)WiFi.macAddress());
  buffer_obj.append("\n");

  this->scan_complete = false;

  //if (scan_mode == WIFI_ARP_SCAN)
  //  this->fullARP();
  
  initTime = millis();
}

void WiFiScan::RunPortScanAll(uint8_t scan_mode, uint16_t color)
{
  if (scan_mode == WIFI_SCAN_SSH)
    startLog("sshscan");
  else if (scan_mode == WIFI_SCAN_TELNET)
    startLog("telnetscan");
  else if (scan_mode == WIFI_SCAN_SMTP)
    startLog("smtp");
  else if (scan_mode == WIFI_SCAN_DNS)
    startLog("dns");
  else if (scan_mode == WIFI_SCAN_HTTP)
    startLog("http");
  else if (scan_mode == WIFI_SCAN_HTTPS)
    startLog("https");
  else if (scan_mode == WIFI_SCAN_RDP)
    startLog("rdp");
  else
    startLog("portscan");

  #ifdef HAS_FLIPPER_LED
    flipper_led.sniffLED();
  #elif defined(XIAO_ESP32_S3)
    xiao_led.sniffLED();
  #elif defined(MARAUDER_M5STICKC)
    stickc_led.sniffLED();
  #else
    led_obj.setMode(MODE_SNIFF);
  #endif
  
  #ifdef HAS_SCREEN
    display_obj.TOP_FIXED_AREA_2 = 48;
    display_obj.tteBar = true;
    display_obj.print_delay_1 = 15;
    display_obj.print_delay_2 = 10;
    display_obj.initScrollValues(true);
    display_obj.tft.setTextWrap(false);
    display_obj.tft.setTextColor(TFT_BLACK, color);
    #ifdef HAS_FULL_SCREEN
      display_obj.tft.fillRect(0,16,TFT_WIDTH,16, color);
      if (scan_mode == WIFI_PORT_SCAN_ALL)
        display_obj.tft.drawCentreString("Port Scan All",TFT_WIDTH / 2,16,2);
      else if (scan_mode == WIFI_SCAN_SSH)
        display_obj.tft.drawCentreString("SSH Scan",TFT_WIDTH / 2,16,2);
      else if (scan_mode == WIFI_SCAN_TELNET)
        display_obj.tft.drawCentreString("Telnet Scan",TFT_WIDTH / 2,16,2);
      else if (scan_mode == WIFI_SCAN_SMTP)
        display_obj.tft.drawCentreString("SMTP Scan",TFT_WIDTH / 2,16,2);
      else if (scan_mode == WIFI_SCAN_DNS)
        display_obj.tft.drawCentreString("DNS Scan",TFT_WIDTH / 2,16,2);
      else if (scan_mode == WIFI_SCAN_HTTP)
        display_obj.tft.drawCentreString("HTTP Scan",TFT_WIDTH / 2,16,2);
      else if (scan_mode == WIFI_SCAN_HTTPS)
        display_obj.tft.drawCentreString("HTTPS Scan",TFT_WIDTH / 2,16,2);
      else if (scan_mode == WIFI_SCAN_RDP)
        display_obj.tft.drawCentreString("RDP Scan",TFT_WIDTH / 2,16,2);
    #endif
    #ifdef HAS_ILI9341
      display_obj.touchToExit();
    #endif
    display_obj.tft.setTextColor(TFT_RED, TFT_BLACK);
    display_obj.setupScrollArea(display_obj.TOP_FIXED_AREA_2, BOT_FIXED_AREA);
  #endif

  this->current_scan_port = 0;
  if ((scan_mode == WIFI_SCAN_SSH) ||
      (scan_mode == WIFI_SCAN_TELNET) ||
      (scan_mode == WIFI_SCAN_SMTP) ||
      (scan_mode == WIFI_SCAN_DNS) ||
      (scan_mode == WIFI_SCAN_HTTP) ||
      (scan_mode == WIFI_SCAN_HTTPS) ||
      (scan_mode == WIFI_SCAN_RDP))
    this->current_scan_ip = this->gateway;

  Serial.println("Starting Port Scan with...");
  Serial.print("IP address: ");
  Serial.println(this->ip_addr);
  Serial.print("Gateway: ");
  Serial.println(this->gateway);
  Serial.print("Netmask: ");
  Serial.println(this->subnet);
  Serial.print("MAC: ");
  Serial.println(WiFi.macAddress());

  buffer_obj.append("Starting Port Scan with...");
  buffer_obj.append("\nSSID: " + (String)this->connected_network);
  buffer_obj.append("\nIP address: ");
  buffer_obj.append(this->ip_addr.toString());
  buffer_obj.append("\nGateway: ");
  buffer_obj.append(this->gateway.toString());
  buffer_obj.append("\nNetmask: ");
  buffer_obj.append(this->subnet.toString());
  buffer_obj.append("\nMAC: ");
  buffer_obj.append((String)WiFi.macAddress());
  buffer_obj.append("\n");

  this->scan_complete = false;
  initTime = millis();
}

void WiFiScan::RunLoadATList() {
  #ifdef HAS_SD
    // Prepare to access the file
    File file = sd_obj.getFile("/Airtags_0.log");
    if (!file) {
      Serial.println("Could not open /Airtags_0.log");
      #ifdef HAS_SCREEN
        display_obj.tft.setTextWrap(false);
        display_obj.tft.setFreeFont(NULL);
        display_obj.tft.setCursor(0, 100);
        display_obj.tft.setTextSize(1);
        display_obj.tft.setTextColor(TFT_CYAN);
      
        display_obj.tft.println("Could not open /Airtags_0.log");
      #endif
      return;
    }

    // Prepare JSON
    DynamicJsonDocument doc(10048);
    DeserializationError error = deserializeJson(doc, file);
    if (error) {
      Serial.print("JSON deserialize error: ");
      Serial.println(error.c_str());
      file.close();
      #ifdef HAS_SCREEN
        display_obj.tft.setTextWrap(false);
        display_obj.tft.setFreeFont(NULL);
        display_obj.tft.setCursor(0, 100);
        display_obj.tft.setTextSize(1);
        display_obj.tft.setTextColor(TFT_CYAN);
      
        display_obj.tft.println("Could not deserialize JSON");
        display_obj.tft.println(error.c_str());
      #endif
      return;
    }

    JsonArray array = doc.as<JsonArray>();
    for (JsonObject obj : array) {
      AirTag at;
      at.mac = obj["mac"].as<String>();
      at.payloadSize = obj["payload_size"];
      at.payload = hexStringToByteArray(obj["payload"].as<String>());
      at.selected = false;
      airtags->add(at);
    }

    file.close();

    //doc.clear();

    #ifdef HAS_SCREEN
      display_obj.tft.setTextWrap(false);
      display_obj.tft.setFreeFont(NULL);
      display_obj.tft.setCursor(0, 100);
      display_obj.tft.setTextSize(1);
      display_obj.tft.setTextColor(TFT_CYAN);
    
      display_obj.tft.print("Loaded Airtags: ");
      display_obj.tft.println((String)airtags->size());
    #endif
    Serial.print("Loaded Airtags:");
    Serial.println((String)airtags->size());
  #endif
}

void WiFiScan::RunSaveATList(bool save_as) {
  #ifdef HAS_SD
    if (save_as) {
      sd_obj.removeFile("/Airtags_0.log");

      this->startLog("Airtags");

      DynamicJsonDocument jsonDocument(2048);

      JsonArray jsonArray = jsonDocument.to<JsonArray>();
      
      for (int i = 0; i < airtags->size(); i++) {
        const AirTag& at = airtags->get(i);
        JsonObject jsonAt = jsonArray.createNestedObject();
        jsonAt["mac"] = at.mac;
        jsonAt["payload"] = byteArrayToHexString(at.payload);
        jsonAt["payload_size"] = at.payloadSize;
      }

      String jsonString;
      serializeJson(jsonArray, jsonString);

      buffer_obj.append(jsonString);

      #ifdef HAS_SCREEN
        display_obj.tft.setTextWrap(false);
        display_obj.tft.setFreeFont(NULL);
        display_obj.tft.setCursor(0, 100);
        display_obj.tft.setTextSize(1);
        display_obj.tft.setTextColor(TFT_CYAN);
      
        display_obj.tft.print("Saved Airtags: ");
        display_obj.tft.println((String)airtags->size());
      #endif
      Serial.print("Saved Airtags:");
      Serial.println((String)airtags->size());
    }
  #endif
}

void WiFiScan::RunLoadAPList() {
  #ifdef HAS_SD
    File file = sd_obj.getFile("/APs_0.log");
    if (!file) {
      Serial.println("Could not open /APs_0.log");
      #ifdef HAS_SCREEN
        display_obj.tft.setTextWrap(false);
        display_obj.tft.setFreeFont(NULL);
        display_obj.tft.setCursor(0, 100);
        display_obj.tft.setTextSize(1);
        display_obj.tft.setTextColor(TFT_CYAN);
        display_obj.tft.println("Could not open /APs_0.log");
      #endif
      return;
    }

    DynamicJsonDocument doc(10048);
    DeserializationError error = deserializeJson(doc, file);
    if (error) {
      Serial.print("JSON deserialize error: ");
      Serial.println(error.c_str());
      file.close();
      #ifdef HAS_SCREEN
        display_obj.tft.setTextWrap(false);
        display_obj.tft.setFreeFont(NULL);
        display_obj.tft.setCursor(0, 100);
        display_obj.tft.setTextSize(1);
        display_obj.tft.setTextColor(TFT_CYAN);
        display_obj.tft.println("Could not deserialize JSON");
        display_obj.tft.println(error.c_str());
      #endif
      return;
    }

    JsonArray array = doc.as<JsonArray>();
    for (JsonObject obj : array) {
      AccessPoint ap;

      ap.essid   = obj.containsKey("essid")   ? obj["essid"].as<String>()      : "";
      ap.channel = obj.containsKey("channel") ? obj["channel"].as<uint8_t>()   : 1;
      ap.selected = false;

      if (obj.containsKey("bssid")) {
        parseBSSID(obj["bssid"], ap.bssid);
      } else {
        memset(ap.bssid, 0, 6); // Zero BSSID if missing
      }

      ap.stations = new LinkedList<uint16_t>();
      ap.rssi     = obj.containsKey("rssi")   ? obj["rssi"].as<int>()          : -127;
      ap.packets  = obj.containsKey("packet") ? obj["packet"].as<uint32_t>()   : 0;
      ap.sec      = obj.containsKey("sec")    ? obj["sec"].as<uint8_t>()       : 0;
      ap.wps      = obj.containsKey("wps")    ? obj["wps"].as<bool>()          : false;
      ap.man      = obj.containsKey("man")    ? obj["man"].as<String>()        : "Unknown";

      access_points->add(ap);
      Serial.println("Got: " + ap.essid);
    }

    file.close();

    #ifdef HAS_SCREEN
      display_obj.tft.setTextWrap(false);
      display_obj.tft.setFreeFont(NULL);
      display_obj.tft.setCursor(0, 100);
      display_obj.tft.setTextSize(1);
      display_obj.tft.setTextColor(TFT_CYAN);
      display_obj.tft.print("Loaded APs: ");
      display_obj.tft.println((String)access_points->size());
    #endif
    Serial.print("Loaded APs:");
    Serial.println((String)access_points->size());
  #endif
}

void WiFiScan::RunSaveAPList(bool save_as) {
  #ifdef HAS_SD
    if (save_as) {
      sd_obj.removeFile("/APs_0.log");

      this->startLog("APs");

      DynamicJsonDocument jsonDocument(2048);

      JsonArray jsonArray = jsonDocument.to<JsonArray>();
      
      for (int i = 0; i < access_points->size(); i++) {
        const AccessPoint& ap = access_points->get(i);
        JsonObject jsonAp = jsonArray.createNestedObject();
        jsonAp["essid"] = ap.essid;
        jsonAp["channel"] = ap.channel;

        char bssidStr[18];
        sprintf(bssidStr, "%02X:%02X:%02X:%02X:%02X:%02X",
                ap.bssid[0], ap.bssid[1], ap.bssid[2],
                ap.bssid[3], ap.bssid[4], ap.bssid[5]);
        jsonAp["bssid"] = bssidStr;
        jsonAp["rssi"] = ap.rssi;
        jsonAp["packets"] = ap.packets;
        jsonAp["sec"] = ap.sec;
        jsonAp["wps"] = ap.wps;
        jsonAp["man"] = ap.man;
      }

      String jsonString;
      serializeJson(jsonArray, jsonString);

      buffer_obj.append(jsonString);

      #ifdef HAS_SCREEN
        display_obj.tft.setTextWrap(false);
        display_obj.tft.setFreeFont(NULL);
        display_obj.tft.setCursor(0, 100);
        display_obj.tft.setTextSize(1);
        display_obj.tft.setTextColor(TFT_CYAN);
      
        display_obj.tft.print("Saved APs: ");
        display_obj.tft.println((String)access_points->size());
      #endif
      Serial.print("Saved APs:");
      Serial.println((String)access_points->size());
    }
  #endif
}

void WiFiScan::RunLoadSSIDList() {
  #ifdef HAS_SD
    File log_file = sd_obj.getFile("/SSIDs_0.log");
    if (!log_file) {
      Serial.println("Could not open /SSIDs_0.log");
      #ifdef HAS_SCREEN
        display_obj.tft.setTextWrap(false);
        display_obj.tft.setFreeFont(NULL);
        display_obj.tft.setCursor(0, 100);
        display_obj.tft.setTextSize(1);
        display_obj.tft.setTextColor(TFT_CYAN);
      
        display_obj.tft.println("Could not open /SSIDs_0.log");
      #endif
      return;
    }
    while (log_file.available()) {
      String line = log_file.readStringUntil('\n'); // Read until newline character
      this->addSSID(line);
    }

    #ifdef HAS_SCREEN
      display_obj.tft.setTextWrap(false);
      display_obj.tft.setFreeFont(NULL);
      display_obj.tft.setCursor(0, 100);
      display_obj.tft.setTextSize(1);
      display_obj.tft.setTextColor(TFT_CYAN);
    
      display_obj.tft.print("Loaded SSIDs: ");
      display_obj.tft.println((String)ssids->size());
    #endif

    log_file.close();

    Serial.print("Loaded SSIDs: ");
    Serial.println((String)ssids->size());
  #endif
}

void WiFiScan::RunSaveSSIDList(bool save_as) {
  #ifdef HAS_SD
    if (save_as) {
      sd_obj.removeFile("/SSIDs_0.log");

      this->startLog("SSIDs");

      for (int i = 0; i < ssids->size(); i++) {
        if (i < ssids->size() - 1)
          buffer_obj.append(ssids->get(i).essid + "\n");
        else
          buffer_obj.append(ssids->get(i).essid);
      }

      #ifdef HAS_SCREEN
        display_obj.tft.setTextWrap(false);
        display_obj.tft.setFreeFont(NULL);
        display_obj.tft.setCursor(0, 100);
        display_obj.tft.setTextSize(1);
        display_obj.tft.setTextColor(TFT_CYAN);
      
        display_obj.tft.print("Saved SSIDs: ");
        display_obj.tft.println((String)ssids->size());
      #endif
      Serial.print("Saved SSIDs: ");
      Serial.println((String)ssids->size());
    }
  #endif
}

void WiFiScan::RunEvilPortal(uint8_t scan_mode, uint16_t color)
{
  startLog("evil_portal");

  #ifdef HAS_FLIPPER_LED
    flipper_led.sniffLED();
  #elif defined(XIAO_ESP32_S3)
    xiao_led.sniffLED();
  #elif defined(MARAUDER_M5STICKC)
    stickc_led.sniffLED();
  #else
    led_obj.setMode(MODE_SNIFF);
  #endif

  #ifdef HAS_SCREEN
    display_obj.TOP_FIXED_AREA_2 = 48;
    display_obj.tteBar = true;
    display_obj.print_delay_1 = 15;
    display_obj.print_delay_2 = 10;
    display_obj.initScrollValues(true);
    display_obj.tft.setTextWrap(false);
    display_obj.tft.setTextColor(TFT_WHITE, color);
    #ifdef HAS_FULL_SCREEN
      display_obj.tft.fillRect(0,16,TFT_WIDTH,16, color);
      display_obj.tft.drawCentreString(" Evil Portal ",TFT_WIDTH / 2,16,2);
    #endif
    #ifdef HAS_ILI9341
      display_obj.touchToExit();
    #endif
    display_obj.tft.setTextColor(TFT_MAGENTA, TFT_BLACK);
    display_obj.setupScrollArea(display_obj.TOP_FIXED_AREA_2, BOT_FIXED_AREA);
  #endif

  #ifdef HAS_DUAL_BAND
    esp_wifi_init(&cfg);
    //esp_wifi_set_country(&country);
  #endif

  evil_portal_obj.begin(ssids, access_points);
  //if (!evil_portal_obj.begin(ssids, access_points)) {
  //  Serial.println("Could not successfully start EvilPortal. Setting WIFI_SCAN_OFF...");
  //  this->StartScan(WIFI_SCAN_OFF, TFT_MAGENTA);
  //  return;
  //}
  //else
  //  Serial.println("Setup EvilPortal. Current mode: " + this->currentScanMode);
  this->wifi_initialized = true;
  initTime = millis();
}

// Function to start running a beacon scan
void WiFiScan::RunAPScan(uint8_t scan_mode, uint16_t color)
{
  if (scan_mode != WIFI_SCAN_AP_STA)
    startPcap("ap");
  else
    startPcap("ap_sta");

  #ifdef HAS_FLIPPER_LED
    flipper_led.sniffLED();
  #elif defined(XIAO_ESP32_S3)
    xiao_led.sniffLED();
  #elif defined(MARAUDER_M5STICKC)
    stickc_led.sniffLED();
  #else
    led_obj.setMode(MODE_SNIFF);
  #endif

  Serial.println(text_table4[9] + (String)access_points->size());
  #ifdef HAS_SCREEN
    display_obj.TOP_FIXED_AREA_2 = 48;
    display_obj.tteBar = true;
    display_obj.print_delay_1 = 15;
    display_obj.print_delay_2 = 10;
    display_obj.initScrollValues(true);
    display_obj.tft.setTextWrap(false);
    if (scan_mode != WIFI_SCAN_AP_STA)
      display_obj.tft.setTextColor(TFT_WHITE, color);
    else
      display_obj.tft.setTextColor(TFT_BLACK, color);
    #ifdef HAS_FULL_SCREEN
      display_obj.tft.fillRect(0,16,TFT_WIDTH,16, color);
      if (scan_mode != WIFI_SCAN_AP_STA)
        display_obj.tft.drawCentreString(text_table4[44],TFT_WIDTH / 2,16,2);
      else
        display_obj.tft.drawCentreString("Scan AP/STA",TFT_WIDTH / 2,16,2);
    #endif
    #ifdef HAS_ILI9341
      display_obj.touchToExit();
    #endif
    display_obj.tft.setTextColor(TFT_GREEN, TFT_BLACK);
    display_obj.setupScrollArea(display_obj.TOP_FIXED_AREA_2, BOT_FIXED_AREA);
  #endif

  delete access_points;
  access_points = new LinkedList<AccessPoint>();

  esp_netif_init();
  esp_event_loop_create_default();

  esp_wifi_init(&cfg2);
  #ifdef HAS_DUAL_BAND
    esp_wifi_set_country(&country);
    esp_event_loop_create_default();
  #endif
  esp_wifi_set_storage(WIFI_STORAGE_RAM);
  esp_wifi_set_mode(WIFI_MODE_NULL);
  esp_wifi_start();
  this->setMac();
  esp_wifi_set_promiscuous(true);
  esp_wifi_set_promiscuous_filter(&filt);
  esp_wifi_set_promiscuous_rx_cb(&apSnifferCallbackFull);
  esp_wifi_set_channel(set_channel, WIFI_SECOND_CHAN_NONE);
  this->wifi_initialized = true;
  initTime = millis();
}

#ifdef HAS_SCREEN
  void WiFiScan::RunLvJoinWiFi(uint8_t scan_mode, uint16_t color) {
  
    #ifdef HAS_TOUCH
      display_obj.tft.init();
      display_obj.tft.setRotation(1);
    #endif
    
    #ifndef HAS_CYD_TOUCH
      display_obj.setCalData(true);
    #else
      //display_obj.touchscreen.setRotation(1);
    #endif
    
    #ifdef HAS_TOUCH
      lv_obj_t * scr = lv_cont_create(NULL, NULL);
      lv_disp_load_scr(scr);
    #endif
  
  }
#endif

void WiFiScan::RunClearStations() {
  #ifdef HAS_SCREEN
    display_obj.tft.setTextWrap(false);
    display_obj.tft.setFreeFont(NULL);
    display_obj.tft.setCursor(0, 100);
    display_obj.tft.setTextSize(1);
    display_obj.tft.setTextColor(TFT_CYAN);
  
    display_obj.tft.println(F(text_table4[45]));
    display_obj.tft.println(text_table4[46] + (String)this->clearStations());
  #else
    this->clearStations();
  #endif
}

void WiFiScan::RunClearAPs() {
  #ifdef HAS_SCREEN
    display_obj.tft.setTextWrap(false);
    display_obj.tft.setFreeFont(NULL);
    display_obj.tft.setCursor(0, 100);
    display_obj.tft.setTextSize(1);
    display_obj.tft.setTextColor(TFT_CYAN);
  
    display_obj.tft.println(F(text_table4[9]));
    display_obj.tft.println(text_table4[10] + (String)this->clearAPs());
    display_obj.tft.println(F(text_table4[45]));
    display_obj.tft.println(text_table4[46] + (String)this->clearStations());
  #else
    this->clearAPs();
    this->clearStations();
  #endif
}

void WiFiScan::RunClearSSIDs() {
  #ifdef HAS_SCREEN
    display_obj.tft.setTextWrap(false);
    display_obj.tft.setFreeFont(NULL);
    display_obj.tft.setCursor(0, 100);
    display_obj.tft.setTextSize(1);
    display_obj.tft.setTextColor(TFT_CYAN);
  
    display_obj.tft.println(F(text_table4[11]));
    display_obj.tft.println(text_table4[12] + (String)this->clearSSIDs());
  #else
    this->clearSSIDs();
  #endif
}

void WiFiScan::setMac() {
  wifi_mode_t currentWiFiMode;
  esp_wifi_get_mode(&currentWiFiMode);
  esp_err_t result;
  result = esp_wifi_set_mac(WIFI_IF_AP, this->ap_mac);
  if ((result != ESP_OK) &&
      ((currentWiFiMode == WIFI_MODE_AP) || (currentWiFiMode == WIFI_MODE_APSTA) || (currentWiFiMode == WIFI_MODE_NULL)))
        Serial.printf("Failed to set AP MAC: %s | 0x%X\n", macToString(this->ap_mac), result);
  else if ((currentWiFiMode == WIFI_MODE_AP) || (currentWiFiMode == WIFI_MODE_APSTA) || (currentWiFiMode == WIFI_MODE_NULL))
    Serial.println("Successfully set AP MAC: " + macToString(this->ap_mac));

  // Do the station  
  result = esp_wifi_set_mac(WIFI_IF_STA, this->sta_mac);
  if ((result != ESP_OK) &&
      ((currentWiFiMode == WIFI_MODE_STA) || (currentWiFiMode == WIFI_MODE_APSTA)))
        Serial.printf("Failed to set STA MAC: %s | 0x%X\n", macToString(this->sta_mac), result);
  else if ((currentWiFiMode == WIFI_MODE_STA) || (currentWiFiMode == WIFI_MODE_APSTA))
    Serial.println("Successfully set STA MAC: " + macToString(this->sta_mac));
}

void WiFiScan::RunSetMac(uint8_t * mac, bool ap) {
  if (ap) {
    for (int i = 0; i < 6; i++) {
      this->ap_mac[i] = mac[i];
    }
  }
  else {
    for (int i = 0; i < 6; i++) {
      this->sta_mac[i] = mac[i];
    }
  }

  if (ap) Serial.println("Setting AP MAC: " + macToString(this->ap_mac));
  else Serial.println("Setting STA MAC: " + macToString(this->sta_mac));

  #ifdef HAS_SCREEN
    display_obj.tft.setTextWrap(false);
    display_obj.tft.setFreeFont(NULL);
    display_obj.tft.setCursor(0, 100);
    display_obj.tft.setTextSize(1);
    display_obj.tft.setTextColor(TFT_CYAN, TFT_BLACK);
    if (ap) display_obj.tft.println("Setting AP MAC: " + macToString(this->ap_mac));
    else display_obj.tft.println("Setting STA MAC: " + macToString(this->sta_mac));
  #endif
}

void WiFiScan::RunGenerateRandomMac(bool ap) {
  if (ap) generateRandomMac(this->ap_mac);
  else generateRandomMac(this->sta_mac);

  if (ap) Serial.println("Setting AP MAC: " + macToString(this->ap_mac));
  else Serial.println("Setting STA MAC: " + macToString(this->sta_mac));

  #ifdef HAS_SCREEN
    display_obj.tft.setTextWrap(false);
    display_obj.tft.setFreeFont(NULL);
    display_obj.tft.setCursor(0, 100);
    display_obj.tft.setTextSize(1);
    display_obj.tft.setTextColor(TFT_CYAN, TFT_BLACK);
    if (ap) display_obj.tft.println("Setting AP MAC: " + macToString(this->ap_mac));
    else display_obj.tft.println("Setting STA MAC: " + macToString(this->sta_mac));
  #endif
}

void WiFiScan::RunGenerateSSIDs(int count) {
  #ifdef HAS_SCREEN
    display_obj.tft.setTextWrap(false);
    display_obj.tft.setFreeFont(NULL);
    display_obj.tft.setCursor(0, 100);
    display_obj.tft.setTextSize(1);
    display_obj.tft.setTextColor(TFT_CYAN);
  
    display_obj.tft.println(F(text_table4[13]));
  
    display_obj.tft.println(text_table4[14] + (String)this->generateSSIDs());
    display_obj.tft.println(text_table4[15] + (String)ssids->size());
  #else
    this->generateSSIDs(count);
  #endif
}

void WiFiScan::logPoint(String lat, String lon, float alt, String datetime, bool poi) {
  datetime.replace(" ", "T");
  datetime += "Z";

  if (!poi)
    buffer_obj.append("    <trkpt lat=\"" + lat + "\" lon=\"" + lon + "\">\n");
  else
    buffer_obj.append("    <wpt lat=\"" + lat + "\" lon=\"" + lon + "\">\n");
  buffer_obj.append("      <ele>" + String(alt, 2) + "</ele>\n");
  buffer_obj.append("      <time>" + datetime + "</time>\n");
  if (!poi)
    buffer_obj.append("    </trkpt>\n");
  else
    buffer_obj.append("    </wpt>\n");
  //gpxFile.flush();
}

void WiFiScan::writeHeader(bool poi) {
  Serial.println("Writing header to GPX file...");
  buffer_obj.append("<?xml version=\"1.0\" encoding=\"UTF-8\"?>\n");
  buffer_obj.append("<gpx version=\"1.1\" creator=\"ESP32 GPS Logger\" xmlns=\"http://www.topografix.com/GPX/1/1\">\n");
  if (!poi)
    buffer_obj.append("  <trk>\n");
  buffer_obj.append("    <name>ESP32 Track</name>\n");
  if (!poi)
    buffer_obj.append("    <trkseg>\n");
}

void WiFiScan::writeFooter(bool poi) {
  Serial.println("Writing footer to GPX file...\n");
  if (!poi) {
    buffer_obj.append("    </trkseg>\n");
    buffer_obj.append("  </trk>\n");
  }
  buffer_obj.append("</gpx>\n");
}

void WiFiScan::RunSetupGPSTracker(uint8_t scan_mode) {
  if (scan_mode == GPS_TRACKER)
    this->startGPX("tracker");
  else if (scan_mode == GPS_POI)
    this->startGPX("poi");

  this->writeHeader(scan_mode == GPS_POI);
  initTime = millis();
}

bool WiFiScan::RunGPSInfo(bool tracker, bool display, bool poi) {
  bool return_val = true;
  #ifdef HAS_GPS
    String text=gps_obj.getText();

    if (tracker) {
      if (gps_obj.getFixStatus()) {
        this->logPoint(gps_obj.getLat(), gps_obj.getLon(), gps_obj.getAlt(), gps_obj.getDatetime(), poi);
      }
      else
        return_val = false;
    }

    if (display) {
      Serial.println("Refreshing GPS Data on screen...");
      #ifdef HAS_SCREEN

        // Get screen position ready
        display_obj.tft.setTextWrap(false);
        display_obj.tft.setFreeFont(NULL);
        display_obj.tft.setCursor(0, SCREEN_HEIGHT / 3);
        display_obj.tft.setTextSize(1);
        display_obj.tft.setTextColor(TFT_CYAN);

        // Clean up screen first
        //display_obj.tft.fillRect(0, 0, 240, STATUS_BAR_WIDTH, STATUSBAR_COLOR);
        display_obj.tft.fillRect(0, (SCREEN_HEIGHT / 3) - 6, SCREEN_WIDTH, SCREEN_HEIGHT - ((SCREEN_HEIGHT / 3) - 6), TFT_BLACK);

        // Print the GPS data: 3
        display_obj.tft.setCursor(0, SCREEN_HEIGHT / 3);
        if (gps_obj.getFixStatus())
          display_obj.tft.println("  Good Fix: Yes");
        else {
          return_val = false;
          display_obj.tft.println("  Good Fix: No");
        }
          
        if(text != "") display_obj.tft.println("      Text: " + text);

        display_obj.tft.println("Satellites: " + gps_obj.getNumSatsString());
        display_obj.tft.println("  Accuracy: " + (String)gps_obj.getAccuracy());
        display_obj.tft.println("  Latitude: " + gps_obj.getLat());
        display_obj.tft.println(" Longitude: " + gps_obj.getLon());
        display_obj.tft.println("  Altitude: " + (String)gps_obj.getAlt());
        display_obj.tft.println("  Datetime: " + gps_obj.getDatetime());
      #endif

      // Display to serial
      Serial.println("==== GPS Data ====");
      if (gps_obj.getFixStatus())
        Serial.println("  Good Fix: Yes");
      else
        Serial.println("  Good Fix: No");
        
      if(text != "") Serial.println("      Text: " + text);

      Serial.println("Satellites: " + gps_obj.getNumSatsString());
      Serial.println("  Accuracy: " + (String)gps_obj.getAccuracy());
      Serial.println("  Latitude: " + gps_obj.getLat());
      Serial.println(" Longitude: " + gps_obj.getLon());
      Serial.println("  Altitude: " + (String)gps_obj.getAlt());
      Serial.println("  Datetime: " + gps_obj.getDatetime());
    }
  #endif

  return return_val;
}

void WiFiScan::RunGPSNmea() {
  #ifdef HAS_GPS
    LinkedList<nmea_sentence_t> *buffer=gps_obj.get_queue();
    bool queue_enabled=gps_obj.queue_enabled();

    String gxgga = gps_obj.generateGXgga();
    String gxrmc = gps_obj.generateGXrmc();

    if(!buffer||!queue_enabled)
      gps_obj.flush_queue();
    #ifndef HAS_SCREEN
      else
        gps_obj.flush_text();
    #else
      // Get screen position ready
      int offset=100;
      if((SCREEN_HEIGHT / 3)<offset)
        offset=SCREEN_HEIGHT/3; //for smaller screens
      if(offset<(TOP_FIXED_AREA+6))
        offset=TOP_FIXED_AREA+6; //absolute minimium
      display_obj.tft.setTextWrap(false);
      display_obj.tft.setFreeFont(NULL);
      display_obj.tft.setCursor(0, offset);
      display_obj.tft.setTextSize(1);
      display_obj.tft.setTextColor(TFT_GREEN);

      // Clean up screen first
      display_obj.tft.fillRect(0, offset-6, SCREEN_WIDTH, SCREEN_HEIGHT - (offset-6), TFT_BLACK);

      #ifdef GPS_NMEA_SCRNLINES
        int lines=GPS_NMEA_SCRNLINES;
      #else
        int lines=TEXT_HEIGHT;
        if(lines>((TFT_HEIGHT-offset-BOT_FIXED_AREA)/10))
          lines=(TFT_HEIGHT-offset-BOT_FIXED_AREA)/10;
      #endif

      String text=gps_obj.getText();
      if(queue_enabled){
        int queue=gps_obj.getTextQueueSize();
        if(queue>0){
          display_obj.tft.println(gps_obj.getTextQueue());
          lines-=queue; //used lines for text display
        }
        else
          if(text != ""){
            display_obj.tft.println(text);
            lines--;
          }
      }
      else
        if(text != ""){
          display_obj.tft.println(text);
          lines--;
        }

      #if GPS_NMEA_SCRNWRAP
        lines-=((gxgga.length()-1)/STANDARD_FONT_CHAR_LIMIT) + 1;
        lines-=((gxrmc.length()-1)/STANDARD_FONT_CHAR_LIMIT) + 1;
        display_obj.tft.setTextWrap(GPS_NMEA_SCRNWRAP);
      #else
        lines-=2; //two self-genned messages
      #endif
    #endif

    if(buffer && queue_enabled){
      int size=buffer->size();
      if(size){
        gps_obj.new_queue();
        for(int i=0;i<size;i++){
          nmea_sentence_t line=buffer->get(i);
          Serial.println(line.sentence);

          #ifdef HAS_SCREEN
            if(lines>0){
              if(line.unparsed){
                if(line.type != "" && line.type != "TXT" && line.type != "GGA" && line.type != "RMC"){
                  int length=line.sentence.length();
                  if(length){
                    #if GPS_NMEA_SCRNWRAP
                      if((((length-1)/STANDARD_FONT_CHAR_LIMIT) + 1)<=lines){
                    #endif
                        display_obj.tft.println(line.sentence);
                        #if GPS_NMEA_SCRNWRAP
                          lines-=((length-1)/STANDARD_FONT_CHAR_LIMIT) + 1;
                        #else
                          lines--;
                        #endif
                    #if GPS_NMEA_SCRNWRAP
                      }
                    #endif
                  }
                }
              }
            }
          #endif
        }
        delete buffer;
      }
    } else {
      static String old_nmea_sentence="";
      String nmea_sentence=gps_obj.getNmeaNotimp();

      if(nmea_sentence != "" && nmea_sentence != old_nmea_sentence){
        old_nmea_sentence=nmea_sentence;
        Serial.println(nmea_sentence);
      }

      #ifdef HAS_SCREEN
        if(lines>0){
          String display_nmea_sentence=gps_obj.getNmeaNotparsed();
          int length=display_nmea_sentence.length();
          if(length)
            #if GPS_NMEA_SCRNWRAP
              if((((length-1)/STANDARD_FONT_CHAR_LIMIT) + 1)<=lines)
            #endif
                display_obj.tft.println(display_nmea_sentence);
        }
      #endif
    }

    #ifdef HAS_SCREEN
      display_obj.tft.println(gxgga);
      display_obj.tft.println(gxrmc);
      #if GPS_NMEA_SCRNWRAP
        display_obj.tft.setTextWrap(false);
      #endif
    #endif

    gps_obj.sendSentence(Serial, gxgga.c_str());
    gps_obj.sendSentence(Serial, gxrmc.c_str());

  #endif
}

void WiFiScan::RunAPInfo(uint16_t index, bool do_display) {
  #ifdef HAS_SCREEN
    if (do_display) {
      display_obj.tft.setCursor(0, (STATUS_BAR_WIDTH * 2) + CHAR_WIDTH + KEY_H);
      display_obj.tft.setTextSize(1);
      display_obj.tft.setTextColor(TFT_WHITE, TFT_BLACK);
    }
  #endif

  Serial.println("   ESSID: " + (String)access_points->get(index).essid);
  Serial.println("   BSSID: " + (String)macToString(access_points->get(index).bssid));
  Serial.println(" Channel: " + (String)access_points->get(index).channel);
  Serial.println("    RSSI: " + (String)access_points->get(index).rssi);
  Serial.println("  Frames: " + (String)access_points->get(index).packets);
  Serial.println("Stations: " + (String)access_points->get(index).stations->size());
  Serial.println("   Brand: " + (String)access_points->get(index).man);
  
  uint8_t sec = access_points->get(index).sec;
  bool wps = access_points->get(index).wps;

  Serial.print("Security: ");
  switch (sec) {
    case WIFI_SECURITY_OPEN:             Serial.println("Open"); break;
    case WIFI_SECURITY_WEP:              Serial.println("WEP"); break;
    case WIFI_SECURITY_WPA:              Serial.println("WPA"); break;
    case WIFI_SECURITY_WPA2:             Serial.println("WPA2"); break;
    case WIFI_SECURITY_WPA3:             Serial.println("WPA3"); break;
    case WIFI_SECURITY_WPA_WPA2_MIXED:   Serial.println("WPA/WPA2 Mixed"); break;
    case WIFI_SECURITY_WPA2_ENTERPRISE:  Serial.println("WPA2 Enterprise"); break;
    case WIFI_SECURITY_WPA3_ENTERPRISE:  Serial.println("WPA3 Enterprise"); break;
    case WIFI_SECURITY_WAPI:             Serial.println("WAPI"); break;
    default:                             Serial.println("Unknown"); break;
  }

  Serial.print("     WPS: ");
  switch (wps) {
    case true:                           Serial.println("true"); break;
    case false:                          Serial.println("false"); break;
    default:                             Serial.println("false"); break;
  }

  #ifdef HAS_SCREEN
    if (do_display) {
      display_obj.tft.println("   ESSID: " + (String)access_points->get(index).essid);
      display_obj.tft.println("   BSSID: " + (String)macToString(access_points->get(index).bssid));
      display_obj.tft.println(" Channel: " + (String)access_points->get(index).channel);
      display_obj.tft.println("    RSSI: " + (String)access_points->get(index).rssi);
      display_obj.tft.println("  Frames: " + (String)access_points->get(index).packets);
      display_obj.tft.println("Stations: " + (String)access_points->get(index).stations->size());
      display_obj.tft.println("   Brand: " + (String)access_points->get(index).man);

      display_obj.tft.print("Security: ");
      switch (sec) {
        case WIFI_SECURITY_OPEN:             display_obj.tft.println("Open"); break;
        case WIFI_SECURITY_WEP:              display_obj.tft.println("WEP"); break;
        case WIFI_SECURITY_WPA:              display_obj.tft.println("WPA"); break;
        case WIFI_SECURITY_WPA2:             display_obj.tft.println("WPA2"); break;
        case WIFI_SECURITY_WPA3:             display_obj.tft.println("WPA3"); break;
        case WIFI_SECURITY_WPA_WPA2_MIXED:   display_obj.tft.println("WPA/WPA2 Mixed"); break;
        case WIFI_SECURITY_WPA2_ENTERPRISE:  display_obj.tft.println("WPA2 Enterprise"); break;
        case WIFI_SECURITY_WPA3_ENTERPRISE:  display_obj.tft.println("WPA3 Enterprise"); break;
        case WIFI_SECURITY_WAPI:             display_obj.tft.println("WAPI"); break;
        default:                             display_obj.tft.println("Unknown"); break;
      }

      display_obj.tft.print("     WPS: ");
      switch (wps) {
        case true:                           display_obj.tft.println("true"); break;
        case false:                          display_obj.tft.println("false"); break;
        default:                             display_obj.tft.println("false"); break;
      }
    }
  #endif

  if (!access_points->get(index).selected) {
    Serial.println("Selected: false");
    #ifdef HAS_SCREEN
      if (do_display) {
        display_obj.tft.println("Selected: false");
      }
    #endif
  }
  else {
    Serial.println("Selected: true");
    #ifdef HAS_SCREEN
      if (do_display) {
        display_obj.tft.println("Selected: true");
      }
    #endif
  }

}

void WiFiScan::RunInfo()
{
  String sta_mac = this->getStaMAC();
  String ap_mac = this->getApMAC();
  String free_ram = this->freeRAM();

  Serial.println(free_ram);

  #ifdef HAS_SCREEN
    display_obj.tft.setTextWrap(false);
    display_obj.tft.setFreeFont(NULL);
    display_obj.tft.setCursor(0, SCREEN_HEIGHT / 3);
    display_obj.tft.setTextSize(1);
    display_obj.tft.setTextColor(TFT_CYAN);
    display_obj.tft.println(text_table4[20]);
    display_obj.tft.println(text_table4[21] + display_obj.version_number);
    display_obj.tft.println("Hardware: " + (String)HARDWARE_NAME);
    display_obj.tft.println(text_table4[22] + (String)esp_get_idf_version());
  #endif

  Serial.println(text_table4[20]);
  Serial.println(text_table4[21] + (String)MARAUDER_VERSION);
  Serial.println("Hardware: " + (String)HARDWARE_NAME);
  Serial.println(text_table4[22] + (String)esp_get_idf_version());

  if (this->wsl_bypass_enabled) {
    #ifdef HAS_SCREEN
      display_obj.tft.println(text_table4[23]);
    #endif
    Serial.println(text_table4[23]);
  }
  else {
    #ifdef HAS_SCREEN
      display_obj.tft.println(text_table4[24]);
    #endif
    Serial.println(text_table4[24]);
  }

  #ifdef HAS_SCREEN
    display_obj.tft.println(text_table4[25] + sta_mac);
    display_obj.tft.println(text_table4[26] + ap_mac);
    display_obj.tft.println(text_table4[27] + free_ram);
  #endif
  Serial.println(text_table4[25] + sta_mac);
  Serial.println(text_table4[26] + ap_mac);
  Serial.println(text_table4[27] + free_ram);

  #if defined(HAS_SD)
    if (sd_obj.supported) {
      #ifdef HAS_SCREEN
        display_obj.tft.println(text_table4[28]);
        display_obj.tft.print(text_table4[29]);
        display_obj.tft.print(sd_obj.card_sz);
        display_obj.tft.println("MB");
      #endif
      Serial.println(text_table4[28]);
      Serial.print(text_table4[29]);
      Serial.print(sd_obj.card_sz);
      Serial.println("MB");
    } else {
      #ifdef HAS_SCREEN
        display_obj.tft.println(text_table4[30]);
        display_obj.tft.println(text_table4[31]);
      #endif
      Serial.println(text_table4[30]);
      Serial.println(text_table4[31]);
    }
  #endif

  #ifdef HAS_BATTERY
    battery_obj.battery_level = battery_obj.getBatteryLevel();
    if (battery_obj.i2c_supported) {
      #ifdef HAS_SCREEN
        display_obj.tft.println(text_table4[32]);
        display_obj.tft.println(text_table4[33] + (String)battery_obj.battery_level + "%");
      #endif
      Serial.println(text_table4[32]);
      Serial.println(text_table4[33] + (String)battery_obj.battery_level + "%");
    }
    else {
      #ifdef HAS_SCREEN
        display_obj.tft.println(text_table4[34]);
      #endif
      Serial.println(text_table4[34]);
    }
  #endif
  
  //#ifdef HAS_SCREEN
  //  display_obj.tft.println(text_table4[35] + (String)temp_obj.current_temp + " C");
  //#endif
}

void WiFiScan::RunPacketMonitor(uint8_t scan_mode, uint16_t color)
{
  #ifdef HAS_FLIPPER_LED
    flipper_led.sniffLED();
  #elif defined(XIAO_ESP32_S3)
    xiao_led.sniffLED();
  #elif defined(MARAUDER_M5STICKC)
    stickc_led.sniffLED();
  #else
    led_obj.setMode(MODE_SNIFF);
  #endif

  if (scan_mode == WIFI_PACKET_MONITOR)
    startPcap("packet_monitor");

  #ifdef HAS_ILI9341
    if ((scan_mode != WIFI_SCAN_PACKET_RATE) &&
        (scan_mode != WIFI_SCAN_CHAN_ANALYZER)) {
      #ifdef HAS_SCREEN
        display_obj.tft.init();
        display_obj.tft.setRotation(1);
        display_obj.tft.fillScreen(TFT_BLACK);
      #endif
    
      #ifdef HAS_SCREEN
        #ifndef HAS_CYD_TOUCH
          display_obj.setCalData(true);
        #else
          //display_obj.touchscreen.setRotation(1);
        #endif
      
        //display_obj.tft.setFreeFont(1);
        display_obj.tft.setFreeFont(NULL);
        display_obj.tft.setTextSize(1);
        display_obj.tft.fillRect(127, 0, 193, 28, TFT_BLACK); // Buttons
        display_obj.tft.fillRect(12, 0, 90, 32, TFT_BLACK); // color key
      
        delay(10);
      
        display_obj.tftDrawGraphObjects(x_scale); //draw graph objects
        display_obj.tftDrawColorKey();
        display_obj.tftDrawXScaleButtons(x_scale);
        display_obj.tftDrawYScaleButtons(y_scale);
        display_obj.tftDrawChannelScaleButtons(set_channel);
        display_obj.tftDrawExitScaleButtons();
      #endif
    }
    else {
      display_obj.TOP_FIXED_AREA_2 = 48;
      display_obj.tteBar = true;
      display_obj.print_delay_1 = 15;
      display_obj.print_delay_2 = 10;
      display_obj.initScrollValues(true);
      display_obj.tft.setTextWrap(false);
      display_obj.tft.setTextColor(TFT_WHITE, color);
      #ifdef HAS_FULL_SCREEN
        display_obj.tft.fillRect(0,16,TFT_WIDTH,16, color);
        if (scan_mode == WIFI_PACKET_MONITOR)
          display_obj.tft.drawCentreString(text_table1[45],TFT_WIDTH / 2,16,2);
        else if (scan_mode == WIFI_SCAN_CHAN_ANALYZER) {
          display_obj.tft.setTextColor(TFT_BLACK, color);
          display_obj.tft.drawCentreString("Channel Analyzer", TFT_WIDTH / 2, 16, 2);
        }
        else if (scan_mode == WIFI_SCAN_PACKET_RATE) {
          display_obj.tft.drawCentreString("Packet Rate", TFT_WIDTH / 2, 16, 2);
        }
      #endif

      // Setup up portrait analyzer buttons
      display_obj.tft.setFreeFont(NULL);
      display_obj.tft.setTextSize(1);
      display_obj.tft.setTextColor(TFT_GREEN, TFT_BLACK);
      display_obj.setupScrollArea(display_obj.TOP_FIXED_AREA_2, BOT_FIXED_AREA);
      display_obj.tftDrawChannelScaleButtons(set_channel, false);
      display_obj.tftDrawExitScaleButtons(false);
    }
  #else // Non touch
    #ifdef HAS_SCREEN
      display_obj.TOP_FIXED_AREA_2 = 48;
      display_obj.tteBar = true;
      display_obj.print_delay_1 = 15;
      display_obj.print_delay_2 = 10;
      display_obj.initScrollValues(true);
      display_obj.tft.setTextWrap(false);
      display_obj.tft.setTextColor(TFT_WHITE, color);
      #ifdef HAS_FULL_SCREEN
        display_obj.tft.fillRect(0,16,TFT_WIDTH,16, color);
        if (scan_mode == WIFI_PACKET_MONITOR)
          display_obj.tft.drawCentreString(text_table1[45],TFT_WIDTH / 2,16,2);
        else if (scan_mode == WIFI_SCAN_CHAN_ANALYZER)
          display_obj.tft.drawCentreString("Channel Analyzer", TFT_WIDTH / 2, 16, 2);
        else if (scan_mode == WIFI_SCAN_PACKET_RATE)
          display_obj.tft.drawCentreString("Packet Rate", TFT_WIDTH / 2, 16, 2);
      #endif
      #ifdef HAS_ILI9341
        display_obj.touchToExit();
      #endif
      display_obj.tft.setTextColor(TFT_GREEN, TFT_BLACK);
      display_obj.setupScrollArea(display_obj.TOP_FIXED_AREA_2, BOT_FIXED_AREA);
    #endif
  #endif

  Serial.println("Running packet scan...");
  esp_wifi_init(&cfg2);
  #ifdef HAS_DUAL_BAND
    esp_wifi_set_country(&country);
    esp_event_loop_create_default();
  #endif
  esp_wifi_set_storage(WIFI_STORAGE_RAM);
  esp_wifi_set_mode(WIFI_MODE_NULL);
  esp_wifi_start();
  this->setMac();
  esp_wifi_set_promiscuous(true);
  esp_wifi_set_promiscuous_filter(&filt);
  esp_wifi_set_promiscuous_rx_cb(&wifiSnifferCallback);
  esp_wifi_set_channel(set_channel, WIFI_SECOND_CHAN_NONE);
  this->wifi_initialized = true;
  uint32_t initTime = millis();
}

void WiFiScan::RunEapolScan(uint8_t scan_mode, uint16_t color)
{
  #ifdef HAS_FLIPPER_LED
    flipper_led.sniffLED();
  #elif defined(XIAO_ESP32_S3)
    xiao_led.sniffLED();
  #elif defined(MARAUDER_M5STICKC)
    stickc_led.sniffLED();
  #else
    led_obj.setMode(MODE_SNIFF);
  #endif
  
  num_eapol = 0;

  #ifdef HAS_ILI9341
    #ifdef HAS_SCREEN
      display_obj.tft.init();
      display_obj.tft.setRotation(1);
      display_obj.tft.fillScreen(TFT_BLACK);
    #endif
  
    startPcap("eapol");
  
    #ifdef HAS_SCREEN
      #ifndef HAS_CYD_TOUCH
        display_obj.setCalData(true);
      #else
        //display_obj.touchscreen.setRotation(1);
      #endif
    
      display_obj.tft.setFreeFont(NULL);
      display_obj.tft.setTextSize(1);
      display_obj.tft.fillRect(127, 0, 193, 28, TFT_BLACK); // Buttons
      display_obj.tft.fillRect(12, 0, 90, 32, TFT_BLACK); // color key
    
      delay(10);
    
      display_obj.tftDrawGraphObjects(x_scale); //draw graph objects
      display_obj.tftDrawEapolColorKey(this->filterActive());
      display_obj.tftDrawChannelScaleButtons(set_channel);
      display_obj.tftDrawExitScaleButtons();
    #endif
  #else
    startPcap("eapol");
    
    #ifdef HAS_SCREEN
      display_obj.TOP_FIXED_AREA_2 = 48;
      display_obj.tteBar = true;
      display_obj.print_delay_1 = 15;
      display_obj.print_delay_2 = 10;
      display_obj.initScrollValues(true);
      display_obj.tft.setTextWrap(false);
      display_obj.tft.setTextColor(TFT_WHITE, color);
      #ifdef HAS_FULL_SCREEN
        display_obj.tft.fillRect(0,16,TFT_WIDTH,16, color);
        display_obj.tft.drawCentreString(text_table4[38],TFT_WIDTH / 2,16,2);
      #endif
      #ifdef HAS_ILI9341
        display_obj.touchToExit();
      #endif
      display_obj.tft.setTextColor(TFT_GREEN, TFT_BLACK);
      display_obj.setupScrollArea(display_obj.TOP_FIXED_AREA_2, BOT_FIXED_AREA);
    #endif
  #endif

  esp_wifi_init(&cfg);
  #ifdef HAS_DUAL_BAND
    esp_wifi_set_country(&country);
    esp_event_loop_create_default();
  #endif
  esp_wifi_set_storage(WIFI_STORAGE_RAM);
  esp_wifi_set_mode(WIFI_MODE_AP);

  esp_err_t err;
  wifi_config_t conf;
  err = esp_wifi_set_protocol(WIFI_IF_AP, WIFI_PROTOCOL_11B | WIFI_PROTOCOL_11G | WIFI_PROTOCOL_11N | WIFI_PROTOCOL_LR);
  if (err != 0)
  {
    Serial.print("could not set protocol : err=0x");
    Serial.println(err, HEX);
  }

  esp_wifi_get_config((wifi_interface_t)WIFI_IF_AP, &conf);
  conf.ap.ssid[0] = '\0';
  conf.ap.ssid_len = 0;
  conf.ap.channel = this->set_channel;
  conf.ap.ssid_hidden = 1;
  conf.ap.max_connection = 0;
  conf.ap.beacon_interval = 60000;

  err = esp_wifi_set_config((wifi_interface_t)WIFI_IF_AP, &conf);
  if (err != 0)
  {
    Serial.print("AP config set error, Maurauder SSID might visible : err=0x");
    Serial.println(err, HEX);
  }

  esp_wifi_start();
  this->setMac();
  esp_wifi_set_promiscuous(true);
  esp_wifi_set_promiscuous_filter(&filt);
  if (scan_mode == WIFI_SCAN_ACTIVE_EAPOL)
    esp_wifi_set_promiscuous_rx_cb(&activeEapolSnifferCallback);
  else if (scan_mode == WIFI_SCAN_ACTIVE_LIST_EAPOL)
    esp_wifi_set_promiscuous_rx_cb(&activeEapolSnifferCallback);
  else
    esp_wifi_set_promiscuous_rx_cb(&eapolSnifferCallback);
  esp_wifi_set_channel(set_channel, WIFI_SECOND_CHAN_NONE);
  this->wifi_initialized = true;
  initTime = millis();
}


// Function to prepare for beacon mimic
void WiFiScan::RunMimicFlood(uint8_t scan_mode, uint16_t color) {
  #ifdef HAS_SCREEN
    display_obj.TOP_FIXED_AREA_2 = 48;
    display_obj.tteBar = true;
    display_obj.print_delay_1 = 15;
    display_obj.print_delay_2 = 10;
    display_obj.initScrollValues(true);
    display_obj.tft.setTextWrap(false);
    display_obj.tft.setTextColor(TFT_BLACK, color);
    #ifdef HAS_FULL_SCREEN
      display_obj.tft.fillRect(0,16,TFT_WIDTH,16, color);
      display_obj.tft.drawCentreString(" Mimic Flood ",TFT_WIDTH / 2,16,2);
    #endif
    #ifdef HAS_ILI9341
      display_obj.touchToExit();
    #endif
    display_obj.tft.setTextColor(TFT_GREEN, TFT_BLACK);
  #endif
  
  packets_sent = 0;
  esp_wifi_init(&cfg);
  #ifdef HAS_DUAL_BAND
    esp_wifi_set_country(&country);
    esp_event_loop_create_default();
  #endif
  esp_wifi_set_storage(WIFI_STORAGE_RAM);
  esp_wifi_set_mode(WIFI_AP_STA);
  esp_wifi_start();
  this->setMac();
  esp_wifi_set_promiscuous_filter(NULL);
  esp_wifi_set_promiscuous(true);
  esp_wifi_set_max_tx_power(78);
  this->wifi_initialized = true;
  initTime = millis();
}

// Pineapple
void WiFiScan::RunPineScan(uint8_t scan_mode, uint16_t color)
{
  this->clearPineScanTrackers();

  startPcap("pinescan");

  #ifdef HAS_FLIPPER_LED
    flipper_led.sniffLED();
  #elif defined(XIAO_ESP32_S3)
    xiao_led.sniffLED();
  #elif defined(MARAUDER_M5STICKC)
    stickc_led.sniffLED();
  #else
    led_obj.setMode(MODE_SNIFF);
  #endif
  
  #ifdef HAS_SCREEN
    display_obj.TOP_FIXED_AREA_2 = 48;
    display_obj.tteBar = true;
    display_obj.print_delay_1 = 15;
    display_obj.print_delay_2 = 10;
    display_obj.initScrollValues(true);
    display_obj.tft.setTextWrap(false);
    display_obj.tft.setTextColor(TFT_BLACK, color);
    #ifdef HAS_FULL_SCREEN
      display_obj.tft.fillRect(0,16,TFT_WIDTH,16, color);
      display_obj.tft.drawCentreString(text_table4[48],TFT_WIDTH / 2,16,2);
    #endif
    #ifdef HAS_ILI9341
      display_obj.touchToExit();
    #endif
    display_obj.tft.setTextColor(TFT_RED, TFT_BLACK);
    display_obj.setupScrollArea(display_obj.TOP_FIXED_AREA_2, BOT_FIXED_AREA);
  #endif
  
  esp_wifi_init(&cfg2);
  #ifdef HAS_DUAL_BAND
    esp_wifi_set_country(&country);
    esp_event_loop_create_default();
  #endif
  esp_wifi_set_storage(WIFI_STORAGE_RAM);
  esp_wifi_set_mode(WIFI_MODE_NULL);
  esp_wifi_start();
  this->setMac();
  esp_wifi_set_promiscuous(true);
  esp_wifi_set_promiscuous_filter(&filt);
  esp_wifi_set_promiscuous_rx_cb(&pineScanSnifferCallback);
  esp_wifi_set_channel(set_channel, WIFI_SECOND_CHAN_NONE);
  this->wifi_initialized = true;
  initTime = millis();
}

// MultiSSID
void WiFiScan::RunMultiSSIDScan(uint8_t scan_mode, uint16_t color)
{
  this->clearMultiSSID();

  startPcap("multissid");

  #ifdef HAS_FLIPPER_LED
    flipper_led.sniffLED();
  #elif defined(XIAO_ESP32_S3)
    xiao_led.sniffLED();
  #elif defined(MARAUDER_M5STICKC)
    stickc_led.sniffLED();
  #else
    led_obj.setMode(MODE_SNIFF);
  #endif
  
  #ifdef HAS_SCREEN
    display_obj.TOP_FIXED_AREA_2 = 48;
    display_obj.tteBar = true;
    display_obj.print_delay_1 = 15;
    display_obj.print_delay_2 = 10;
    display_obj.initScrollValues(true);
    display_obj.tft.setTextWrap(false);
    display_obj.tft.setTextColor(TFT_BLACK, color);
    #ifdef HAS_FULL_SCREEN
      display_obj.tft.fillRect(0,16,TFT_WIDTH,16, color);
      display_obj.tft.drawCentreString(text_table4[49],TFT_WIDTH / 2,16,2);
    #endif
    #ifdef HAS_ILI9341
      display_obj.touchToExit();
    #endif
    display_obj.tft.setTextColor(TFT_BLUE, TFT_BLACK);
    display_obj.setupScrollArea(display_obj.TOP_FIXED_AREA_2, BOT_FIXED_AREA);
  #endif
  
  esp_wifi_init(&cfg2);
  #ifdef HAS_DUAL_BAND
    esp_wifi_set_country(&country);
    esp_event_loop_create_default();
  #endif
  esp_wifi_set_storage(WIFI_STORAGE_RAM);
  esp_wifi_set_mode(WIFI_MODE_NULL);
  esp_wifi_start();
  this->setMac();
  esp_wifi_set_promiscuous(true);
  esp_wifi_set_promiscuous_filter(&filt);
  esp_wifi_set_promiscuous_rx_cb(&multiSSIDSnifferCallback);
  esp_wifi_set_channel(set_channel, WIFI_SECOND_CHAN_NONE);
  this->wifi_initialized = true;
  initTime = millis();
}

void WiFiScan::RunPwnScan(uint8_t scan_mode, uint16_t color)
{
  startPcap("pwnagotchi");

  #ifdef HAS_FLIPPER_LED
    flipper_led.sniffLED();
  #elif defined(XIAO_ESP32_S3)
    xiao_led.sniffLED();
  #elif defined(MARAUDER_M5STICKC)
    stickc_led.sniffLED();
  #else
    led_obj.setMode(MODE_SNIFF);
  #endif

  #ifdef HAS_SCREEN
    display_obj.TOP_FIXED_AREA_2 = 48;
    display_obj.tteBar = true;
    display_obj.print_delay_1 = 15;
    display_obj.print_delay_2 = 10;
    display_obj.initScrollValues(true);
    display_obj.tft.setTextWrap(false);
    display_obj.tft.setTextColor(TFT_WHITE, color);
    #ifdef HAS_FULL_SCREEN
      display_obj.tft.fillRect(0,16,TFT_WIDTH,16, color);
      display_obj.tft.drawCentreString(text_table4[37],TFT_WIDTH / 2,16,2);
    #endif
    #ifdef HAS_ILI9341
      display_obj.touchToExit();
    #endif
    display_obj.tft.setTextColor(TFT_GREEN, TFT_BLACK);
    display_obj.setupScrollArea(display_obj.TOP_FIXED_AREA_2, BOT_FIXED_AREA);
  #endif
  
  esp_wifi_init(&cfg2);
  #ifdef HAS_DUAL_BAND
    esp_wifi_set_country(&country);
    esp_event_loop_create_default();
  #endif
  esp_wifi_set_storage(WIFI_STORAGE_RAM);
  esp_wifi_set_mode(WIFI_MODE_NULL);
  esp_wifi_start();
  this->setMac();
  esp_wifi_set_promiscuous(true);
  esp_wifi_set_promiscuous_filter(&filt);
  esp_wifi_set_promiscuous_rx_cb(&beaconSnifferCallback);
  esp_wifi_set_channel(set_channel, WIFI_SECOND_CHAN_NONE);
  this->wifi_initialized = true;
  initTime = millis();
}

void WiFiScan::executeSourApple() {
  #ifdef HAS_BT
    NimBLEDevice::init("");
    NimBLEServer *pServer = NimBLEDevice::createServer();

    pAdvertising = pServer->getAdvertising();

    delay(40);
    //NimBLEAdvertisementData advertisementData = getOAdvertisementData();
    NimBLEAdvertisementData advertisementData = this->GetUniversalAdvertisementData(Apple);
    pAdvertising->setAdvertisementData(advertisementData);
    pAdvertising->start();
    delay(20);
    pAdvertising->stop();
  #endif
}

void WiFiScan::setBaseMacAddress(uint8_t macAddr[6]) {
  // Use ESP-IDF function to set the base MAC address
  esp_err_t err = esp_base_mac_addr_set(macAddr);

  // Check for success or handle errors
  if (err == ESP_OK) {
    return;
  } else if (err == ESP_ERR_INVALID_ARG) {
    Serial.println("Error: Invalid MAC address argument.");
  } else {
    Serial.printf("Error: Failed to set MAC address. Code: %d\n", err);
  }
}

void WiFiScan::executeSpoofAirtag() {
  #ifdef HAS_BT
    for (int i = 0; i < airtags->size(); i++) {
      if (airtags->get(i).selected) {

        uint8_t macAddr[6];

        convertMacStringToUint8(airtags->get(i).mac, macAddr);

        macAddr[5] -= 2;

        // Do this because ESP32 BT addr is Base MAC + 2
        
        this->setBaseMacAddress(macAddr);

        NimBLEDevice::init("");

        NimBLEServer *pServer = NimBLEDevice::createServer();

        pAdvertising = pServer->getAdvertising();

        //NimBLEAdvertisementData advertisementData = getSwiftAdvertisementData();
        NimBLEAdvertisementData advertisementData = this->GetUniversalAdvertisementData(Airtag);
        pAdvertising->setAdvertisementData(advertisementData);
        pAdvertising->start();
        delay(10);
        pAdvertising->stop();

        NimBLEDevice::deinit();

        break;
      }
    }
  #endif
}

void WiFiScan::executeSwiftpairSpam(EBLEPayloadType type) {
  #ifdef HAS_BT
    uint8_t macAddr[6];
    generateRandomMac(macAddr);

    //esp_base_mac_addr_set(macAddr);

    this->setBaseMacAddress(macAddr);

    NimBLEDevice::init("");

    NimBLEServer *pServer = NimBLEDevice::createServer();

    pAdvertising = pServer->getAdvertising();

    //NimBLEAdvertisementData advertisementData = getSwiftAdvertisementData();
    NimBLEAdvertisementData advertisementData = this->GetUniversalAdvertisementData(type);
    pAdvertising->setAdvertisementData(advertisementData);
    pAdvertising->start();
    delay(10);
    pAdvertising->stop();

    NimBLEDevice::deinit();
  #endif
}

void WiFiScan::executeWarDrive() {
  #ifdef HAS_GPS
    if (gps_obj.getGpsModuleStatus()) {
      bool do_save;
      String display_string;
      
      while (WiFi.scanComplete() == WIFI_SCAN_RUNNING) {
        Serial.println("Scan running...");
        delay(500);
      }
      
      #ifndef HAS_DUAL_BAND
        int n = WiFi.scanNetworks(false, true, false, 110, this->set_channel);
      #else
        int n = WiFi.scanNetworks(false, true, false, 110);
      #endif

      if (n > 0) {
        for (int i = 0; i < n; i++) {
          display_string = "";
          do_save = false;
          uint8_t *this_bssid_raw = WiFi.BSSID(i);
          char this_bssid[18] = {0};
          sprintf(this_bssid, "%02X:%02X:%02X:%02X:%02X:%02X", this_bssid_raw[0], this_bssid_raw[1], this_bssid_raw[2], this_bssid_raw[3], this_bssid_raw[4], this_bssid_raw[5]);

          if (this->seen_mac(this_bssid_raw))
            continue;

          this->save_mac(this_bssid_raw);

          String ssid = WiFi.SSID(i);
          ssid.replace(",","_");

          if (ssid != "") {
            display_string.concat(ssid);
          }
          else {
            display_string.concat(this_bssid);
          }

          if (gps_obj.getFixStatus()) {
            do_save = true;
            display_string.concat(" | Lt: " + gps_obj.getLat());
            display_string.concat(" | Ln: " + gps_obj.getLon());
          }
          else {
            display_string.concat(" | GPS: No Fix");
          }

          int temp_len = display_string.length();

          #ifdef HAS_SCREEN
            for (int i = 0; i < 40 - temp_len; i++)
            {
              display_string.concat(" ");
            }
            
            display_obj.display_buffer->add(display_string);
          #endif


          String wardrive_line = WiFi.BSSIDstr(i) + "," + ssid + "," + this->security_int_to_string(WiFi.encryptionType(i)) + "," + gps_obj.getDatetime() + "," + (String)WiFi.channel(i) + "," + (String)WiFi.RSSI(i) + "," + gps_obj.getLat() + "," + gps_obj.getLon() + "," + gps_obj.getAlt() + "," + gps_obj.getAccuracy() + ",WIFI\n";
          Serial.print((String)this->mac_history_cursor + " | " + wardrive_line);

          if (do_save) {
            buffer_obj.append(wardrive_line);
          }
        }
      }
      this->channelHop();

      // Free up that memory, you sexy devil
      WiFi.scanDelete();
    }
  #endif
}

// Function to start running a beacon scan
void WiFiScan::RunBeaconScan(uint8_t scan_mode, uint16_t color)
{
  if (scan_mode == WIFI_SCAN_AP)
    startPcap("beacon");
  else if (scan_mode == WIFI_SCAN_WAR_DRIVE) {
    #ifdef HAS_GPS
      if (gps_obj.getGpsModuleStatus()) {
        startLog("wardrive");
        String header_line = "WigleWifi-1.4,appRelease=" + (String)MARAUDER_VERSION + ",model=ESP32 Marauder,release=" + (String)MARAUDER_VERSION + ",device=ESP32 Marauder,display=SPI TFT,board=ESP32 Marauder,brand=JustCallMeKoko\nMAC,SSID,AuthMode,FirstSeen,Channel,RSSI,CurrentLatitude,CurrentLongitude,AltitudeMeters,AccuracyMeters,Type\n";
        buffer_obj.append(header_line);
      } else {
        return;
      }
    #else
      return;
    #endif
  }

  #ifdef HAS_FLIPPER_LED
    flipper_led.sniffLED();
  #elif defined(XIAO_ESP32_S3)
    xiao_led.sniffLED();
  #elif defined(MARAUDER_M5STICKC)
    stickc_led.sniffLED();
  #else
    led_obj.setMode(MODE_SNIFF);
  #endif
  
  #ifdef HAS_SCREEN
    display_obj.TOP_FIXED_AREA_2 = 48;
    display_obj.tteBar = true;
    display_obj.print_delay_1 = 15;
    display_obj.print_delay_2 = 10;
    display_obj.initScrollValues(true);
    display_obj.tft.setTextWrap(false);
    display_obj.tft.setTextColor(TFT_WHITE, color);
    #ifdef HAS_FULL_SCREEN
      display_obj.tft.fillRect(0,16,TFT_WIDTH,16, color);
      if (scan_mode == WIFI_SCAN_AP)
        display_obj.tft.drawCentreString(text_table4[38],TFT_WIDTH / 2,16,2);
      else if (scan_mode == WIFI_SCAN_WAR_DRIVE) {
        this->clearMacHistory();
        display_obj.tft.drawCentreString("Wardrive", TFT_WIDTH / 2, 16, 2);
      }
      #ifdef HAS_ILI9341
        display_obj.touchToExit();
      #endif
    #endif
    display_obj.tft.setTextColor(TFT_GREEN, TFT_BLACK);
    display_obj.setupScrollArea(display_obj.TOP_FIXED_AREA_2, BOT_FIXED_AREA);
  #endif

  if (scan_mode != WIFI_SCAN_WAR_DRIVE) {
  
    esp_wifi_init(&cfg2);
    #ifdef HAS_DUAL_BAND
      esp_wifi_set_country(&country);
      esp_event_loop_create_default();
    #endif
    esp_wifi_set_storage(WIFI_STORAGE_RAM);
    esp_wifi_set_mode(WIFI_MODE_NULL);
    esp_wifi_start();
    this->setMac();
    esp_wifi_set_promiscuous(true);
    esp_wifi_set_promiscuous_filter(&filt);
    esp_wifi_set_promiscuous_rx_cb(&beaconSnifferCallback);
    esp_wifi_set_channel(set_channel, WIFI_SECOND_CHAN_NONE);
  }
  else {
    this->startWardriverWiFi();
  }
  this->wifi_initialized = true;
  initTime = millis();
}

void WiFiScan::startWardriverWiFi() {
  WiFi.mode(WIFI_STA);
  WiFi.disconnect();
}

void WiFiScan::RunStationScan(uint8_t scan_mode, uint16_t color)
{
  startPcap("station");

  #ifdef HAS_FLIPPER_LED
    flipper_led.sniffLED();
  #elif defined(XIAO_ESP32_S3)
    xiao_led.sniffLED();
  #elif defined(MARAUDER_M5STICKC)
    stickc_led.sniffLED();
  #else
    led_obj.setMode(MODE_SNIFF);
  #endif
  
  #ifdef HAS_SCREEN
    display_obj.TOP_FIXED_AREA_2 = 48;
    display_obj.tteBar = true;
    display_obj.print_delay_1 = 15;
    display_obj.print_delay_2 = 10;
    display_obj.initScrollValues(true);
    display_obj.tft.setTextWrap(false);
    display_obj.tft.setTextColor(TFT_WHITE, color);
    #ifdef HAS_FULL_SCREEN
      display_obj.tft.fillRect(0,16,TFT_WIDTH,16, color);
      display_obj.tft.drawCentreString(text_table1[59],TFT_WIDTH / 2,16,2);
    #endif
    #ifdef HAS_ILI9341
      display_obj.touchToExit();
    #endif
    display_obj.tft.setTextColor(TFT_GREEN, TFT_BLACK);
    display_obj.setupScrollArea(display_obj.TOP_FIXED_AREA_2, BOT_FIXED_AREA);
  #endif
  
  esp_netif_init();
  esp_event_loop_create_default();
  //esp_wifi_init(&cfg);
  esp_err_t err = esp_wifi_init(&cfg2);
  if (err != ESP_OK) {
    Serial.printf("Custom config failed (0x%04X), falling back to default...\n", err);
    wifi_init_config_t default_cfg = WIFI_INIT_CONFIG_DEFAULT();
    err = esp_wifi_init(&default_cfg);
    if (err != ESP_OK) {
      Serial.printf("Default config also failed (0x%04X)\n", err);
    } else {
      Serial.println("Wi-Fi init succeeded with default config.");
    }
  } else {
    Serial.println("Wi-Fi init succeeded with custom config.");
  }
  #ifdef HAS_DUAL_BAND
    esp_wifi_set_country(&country);
    esp_event_loop_create_default();
  #endif
  esp_wifi_set_storage(WIFI_STORAGE_RAM);
  esp_wifi_set_mode(WIFI_MODE_NULL);
  esp_wifi_start();
  this->setMac();
  esp_wifi_set_promiscuous(true);
  esp_wifi_set_promiscuous_filter(&filt);
  esp_wifi_set_promiscuous_rx_cb(&stationSnifferCallback);
  esp_wifi_set_channel(set_channel, WIFI_SECOND_CHAN_NONE);
  this->wifi_initialized = true;
  initTime = millis();
}

void WiFiScan::RunRawScan(uint8_t scan_mode, uint16_t color)
{
  if (scan_mode != WIFI_SCAN_SIG_STREN)
    startPcap("raw");

  #ifdef HAS_FLIPPER_LED
    flipper_led.sniffLED();
  #elif defined(XIAO_ESP32_S3)
    xiao_led.sniffLED();
  #elif defined(MARAUDER_M5STICKC)
    stickc_led.sniffLED();
  #else
    led_obj.setMode(MODE_SNIFF);
  #endif
  
  #ifdef HAS_SCREEN
    display_obj.TOP_FIXED_AREA_2 = 48;
    display_obj.tteBar = true;
    display_obj.print_delay_1 = 15;
    display_obj.print_delay_2 = 10;
    display_obj.initScrollValues(true);
    display_obj.tft.setTextWrap(false);
    display_obj.tft.setTextColor(TFT_WHITE, color);
    #ifdef HAS_FULL_SCREEN
      display_obj.tft.fillRect(0,16,TFT_WIDTH,16, color);
      if (scan_mode != WIFI_SCAN_SIG_STREN) {
        display_obj.tft.setTextColor(TFT_BLACK, color);
        display_obj.tft.drawCentreString(text_table1[58],TFT_WIDTH / 2,16,2);
      }
      else {
        display_obj.tft.setTextColor(TFT_BLACK, color);
        display_obj.tft.drawCentreString("Signal Monitor", TFT_WIDTH / 2, 16, 2);
      }
    #endif
    display_obj.tft.setTextColor(TFT_GREEN, TFT_BLACK);
    display_obj.setupScrollArea(display_obj.TOP_FIXED_AREA_2, BOT_FIXED_AREA);
    //display_obj.setupScrollArea((STATUS_BAR_WIDTH * 2) + CHAR_WIDTH - 1, BOT_FIXED_AREA);

    #ifdef HAS_ILI9341
      if ((scan_mode == WIFI_SCAN_RAW_CAPTURE) ||
          (scan_mode == WIFI_SCAN_SIG_STREN)) {
        display_obj.tft.setFreeFont(NULL);
        display_obj.tft.setTextSize(1);
        display_obj.tft.setTextColor(TFT_GREEN, TFT_BLACK);
        if (scan_mode != WIFI_SCAN_SIG_STREN)
          display_obj.setupScrollArea(display_obj.TOP_FIXED_AREA_2, BOT_FIXED_AREA);
        else
          display_obj.setupScrollArea((STATUS_BAR_WIDTH * 2) + CHAR_WIDTH - 1, BOT_FIXED_AREA);
        display_obj.tftDrawChannelScaleButtons(set_channel, false);
        display_obj.tftDrawExitScaleButtons(false);
      }
    #endif
  #endif
  
  esp_wifi_init(&cfg2);
  #ifdef HAS_DUAL_BAND
    esp_wifi_set_country(&country);
    esp_event_loop_create_default();
  #endif
  esp_wifi_set_storage(WIFI_STORAGE_RAM);
  esp_wifi_set_mode(WIFI_MODE_NULL);
  esp_wifi_start();
  this->setMac();
  esp_wifi_set_promiscuous(true);
  esp_wifi_set_promiscuous_filter(&filt);
  esp_wifi_set_promiscuous_rx_cb(&rawSnifferCallback);
  esp_wifi_set_channel(set_channel, WIFI_SECOND_CHAN_NONE);
  this->wifi_initialized = true;
  initTime = millis();
}

void WiFiScan::RunDeauthScan(uint8_t scan_mode, uint16_t color)
{
  startPcap("deauth");

  #ifdef HAS_FLIPPER_LED
    flipper_led.sniffLED();
  #elif defined(XIAO_ESP32_S3)
    xiao_led.sniffLED();
  #elif defined(MARAUDER_M5STICKC)
    stickc_led.sniffLED();
  #else
    led_obj.setMode(MODE_SNIFF);
  #endif
  
  #ifdef HAS_SCREEN
    display_obj.TOP_FIXED_AREA_2 = 48;
    display_obj.tteBar = true;
    display_obj.print_delay_1 = 15;
    display_obj.print_delay_2 = 10;
    display_obj.initScrollValues(true);
    display_obj.tft.setTextWrap(false);
    display_obj.tft.setTextColor(TFT_BLACK, color);
    #ifdef HAS_FULL_SCREEN
      display_obj.tft.fillRect(0,16,TFT_WIDTH,16, color);
      display_obj.tft.drawCentreString(text_table4[39],TFT_WIDTH / 2,16,2);
    #endif
    #ifdef HAS_ILI9341
      display_obj.touchToExit();
    #endif
    display_obj.tft.setTextColor(TFT_RED, TFT_BLACK);
    display_obj.setupScrollArea(display_obj.TOP_FIXED_AREA_2, BOT_FIXED_AREA);
  #endif
  
  esp_wifi_init(&cfg2);
  #ifdef HAS_DUAL_BAND
    esp_wifi_set_country(&country);
    esp_event_loop_create_default();
  #endif
  esp_wifi_set_ps(WIFI_PS_NONE);
  esp_wifi_set_storage(WIFI_STORAGE_RAM);
  esp_wifi_set_mode(WIFI_MODE_NULL);  
  esp_wifi_start();
  this->setMac();
  esp_wifi_set_promiscuous(true);
  esp_wifi_set_promiscuous_filter(&filt);
  esp_wifi_set_promiscuous_rx_cb(&deauthSnifferCallback);
  esp_wifi_set_channel(set_channel, WIFI_SECOND_CHAN_NONE);
  this->wifi_initialized = true;
  initTime = millis();
}


// Function for running probe request scan
void WiFiScan::RunProbeScan(uint8_t scan_mode, uint16_t color)
{
  probe_req_ssids->clear();

  if (scan_mode == WIFI_SCAN_PROBE)
    startPcap("probe");
  else if (scan_mode == WIFI_SCAN_STATION_WAR_DRIVE) {
    #ifdef HAS_GPS
      if (gps_obj.getGpsModuleStatus()) {
        startLog("station_wardrive");
        String header_line = "WigleWifi-1.4,appRelease=" + (String)MARAUDER_VERSION + ",model=ESP32 Marauder,release=" + (String)MARAUDER_VERSION + ",device=ESP32 Marauder,display=SPI TFT,board=ESP32 Marauder,brand=JustCallMeKoko\nMAC,SSID,AuthMode,FirstSeen,Channel,RSSI,CurrentLatitude,CurrentLongitude,AltitudeMeters,AccuracyMeters,Type\n";
        buffer_obj.append(header_line);
      } else {
        return;
      }
    #else
      return;
    #endif
  }

  #ifdef HAS_FLIPPER_LED
    flipper_led.sniffLED();
  #elif defined(XIAO_ESP32_S3)
    xiao_led.sniffLED();
  #elif defined(MARAUDER_M5STICKC)
    stickc_led.sniffLED();
  #else
    led_obj.setMode(MODE_SNIFF);
  #endif
  
  #ifdef HAS_SCREEN
    display_obj.TOP_FIXED_AREA_2 = 48;
    display_obj.tteBar = true;
    display_obj.print_delay_1 = 15;
    display_obj.print_delay_2 = 10;
    display_obj.initScrollValues(true);
    display_obj.tft.setTextWrap(false);
    display_obj.tft.setTextColor(TFT_BLACK, color);
    #ifdef HAS_FULL_SCREEN
      display_obj.tft.fillRect(0,16,TFT_WIDTH,16, color);
      display_obj.tft.drawCentreString(text_table4[40],TFT_WIDTH / 2,16,2);
    #endif
    #ifdef HAS_ILI9341
      display_obj.touchToExit();
    #endif
    display_obj.tft.setTextColor(TFT_GREEN, TFT_BLACK);
    display_obj.setupScrollArea(display_obj.TOP_FIXED_AREA_2, BOT_FIXED_AREA);
  #endif
  
  esp_wifi_init(&cfg2);
  #ifdef HAS_DUAL_BAND
    esp_wifi_set_country(&country);
    esp_event_loop_create_default();
  #endif
  esp_wifi_set_storage(WIFI_STORAGE_RAM);
  esp_wifi_set_mode(WIFI_MODE_NULL);
  esp_wifi_start();
  this->setMac();
  esp_wifi_set_promiscuous(true);
  esp_wifi_set_promiscuous_filter(&filt);
  esp_wifi_set_promiscuous_rx_cb(&probeSnifferCallback);
  esp_wifi_set_channel(set_channel, WIFI_SECOND_CHAN_NONE);
  this->wifi_initialized = true;
  initTime = millis();
}

void WiFiScan::RunSourApple(uint8_t scan_mode, uint16_t color) {
  #ifdef HAS_BT
    /*NimBLEDevice::init("");
    NimBLEServer *pServer = NimBLEDevice::createServer();

    pAdvertising = pServer->getAdvertising();*/

    #ifdef HAS_SCREEN
      display_obj.TOP_FIXED_AREA_2 = 48;
      display_obj.tteBar = true;
      display_obj.print_delay_1 = 15;
      display_obj.print_delay_2 = 10;
      display_obj.initScrollValues(true);
      display_obj.tft.setTextWrap(false);
      display_obj.tft.setTextColor(TFT_BLACK, color);
      #ifdef HAS_FULL_SCREEN
        display_obj.tft.fillRect(0,16,TFT_WIDTH,16, color);
        display_obj.tft.drawCentreString("Sour Apple",TFT_WIDTH / 2,16,2);
      #endif
      #ifdef HAS_ILI9341
        display_obj.touchToExit();
      #endif
      display_obj.tft.setTextColor(TFT_GREEN, TFT_BLACK);
    #endif

    #ifdef HAS_FLIPPER_LED
      flipper_led.sniffLED();
    #elif defined(XIAO_ESP32_S3)
      xiao_led.sniffLED();
    #elif defined(MARAUDER_M5STICKC)
      stickc_led.sniffLED();
    #else
      led_obj.setMode(MODE_SNIFF);
    #endif

  #endif
}
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
